mpogue2/ladybug-mixer/docs/3.5mm stereo jacks.png

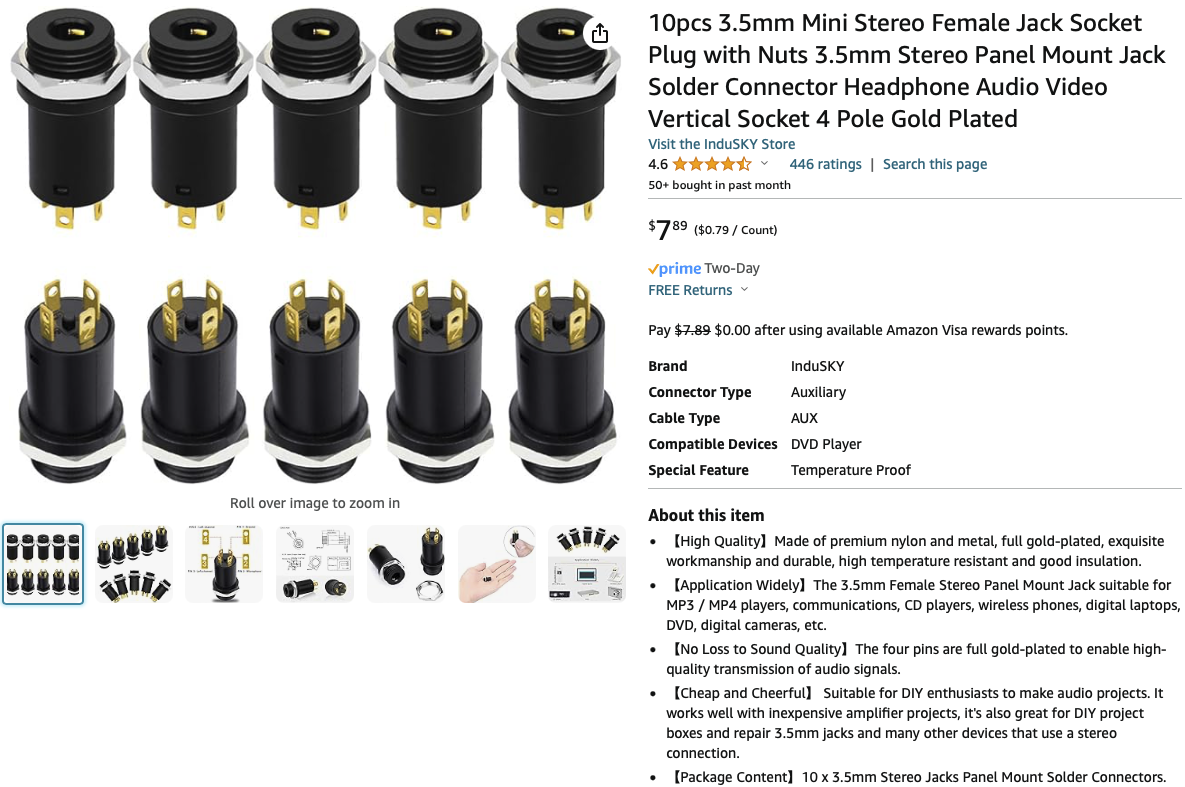
docs/3.5mm stereo jacks.png
