mpogue2/ladybug-mixer/docs/9V Battery Box.png

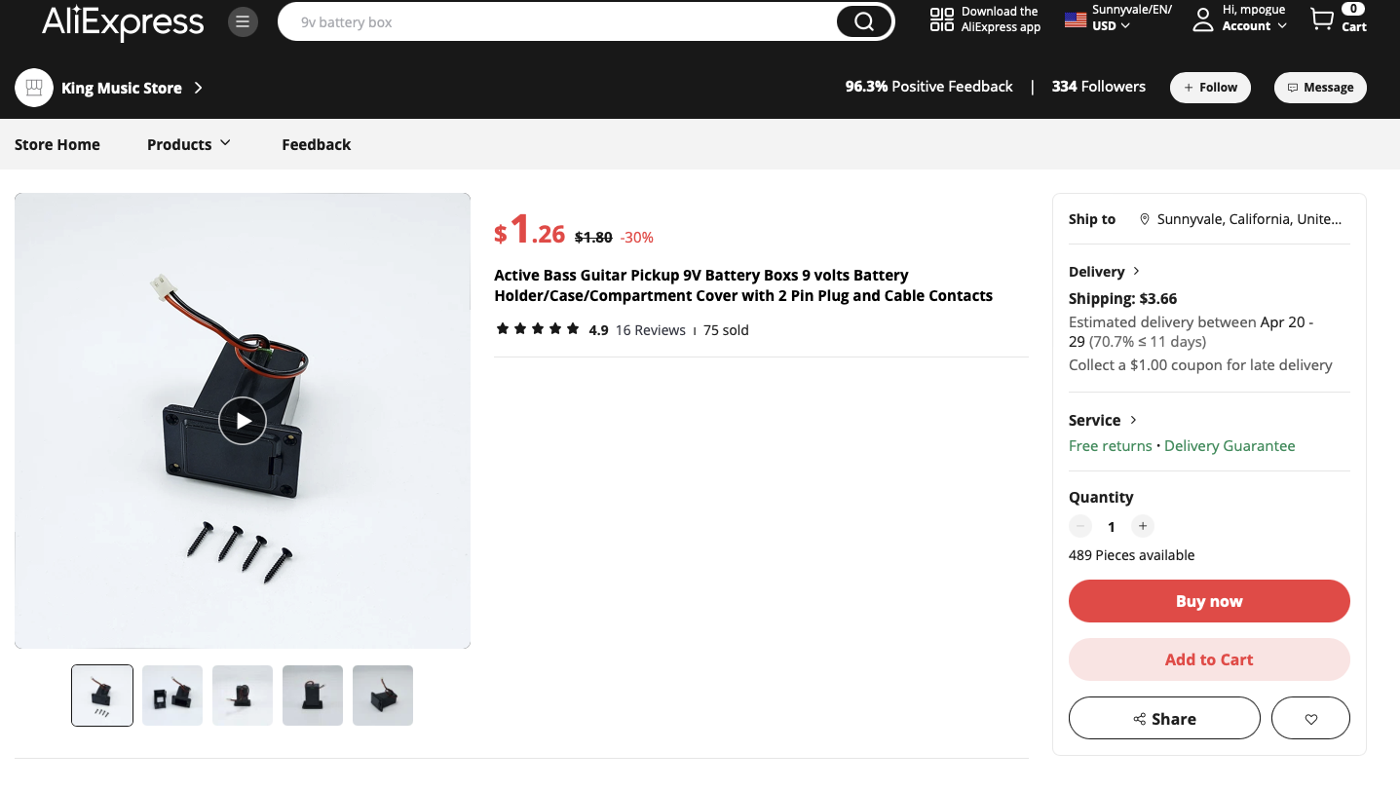
docs/9V Battery Box.png
