mpogue2/ladybug-mixer/docs/100K pots.png

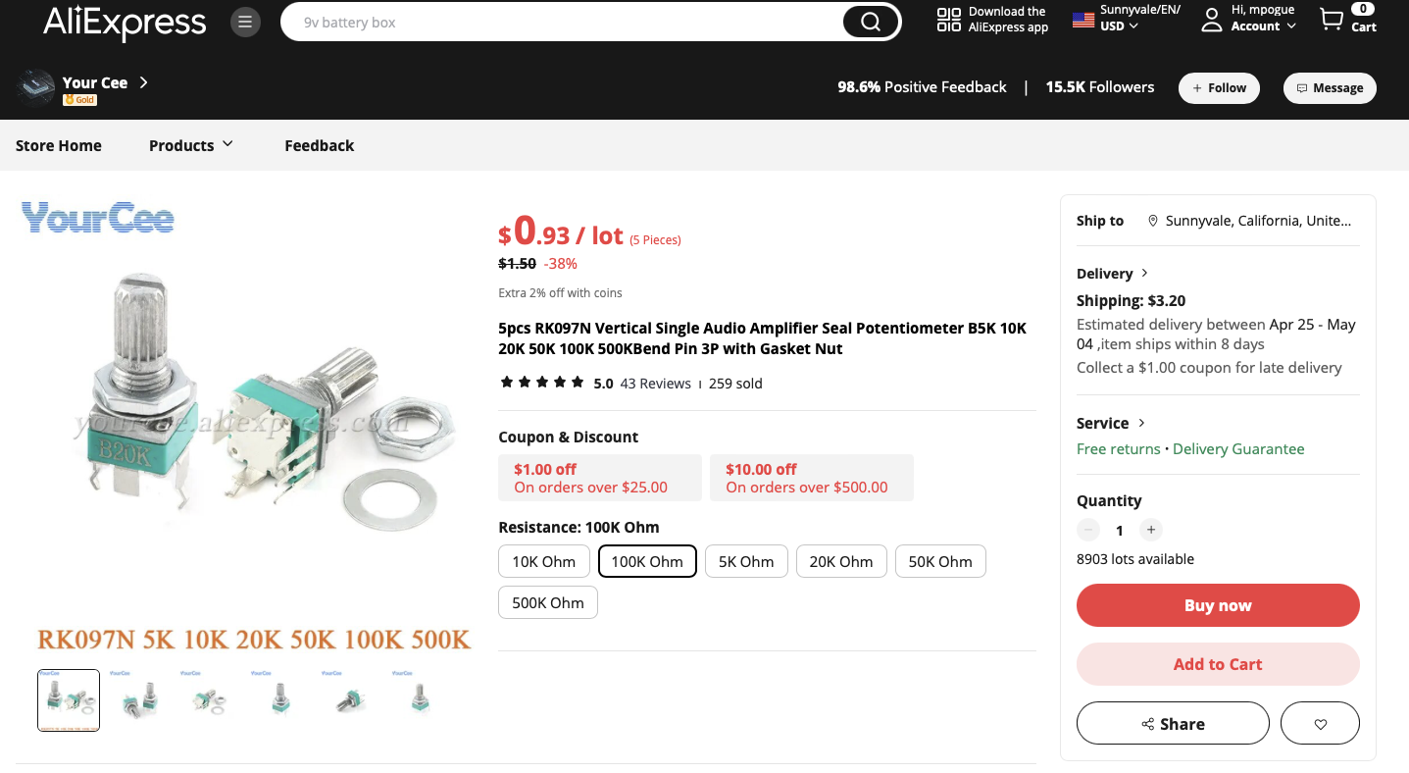
docs/100K pots.png
