mpogue2/ladybug-mixer/docs/AMZN Basics 9V Alkaline batteries.png

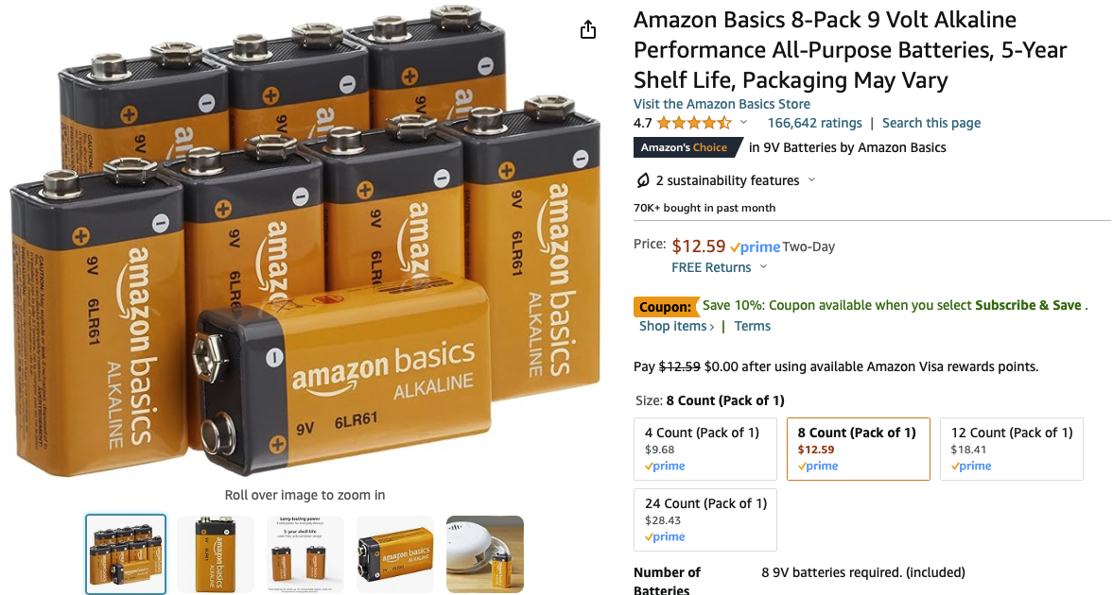
docs/AMZN Basics 9V Alkaline batteries.png
