mpogue2/ladybug-mixer/docs/Neutrik NC3MAV-0 output connector.png

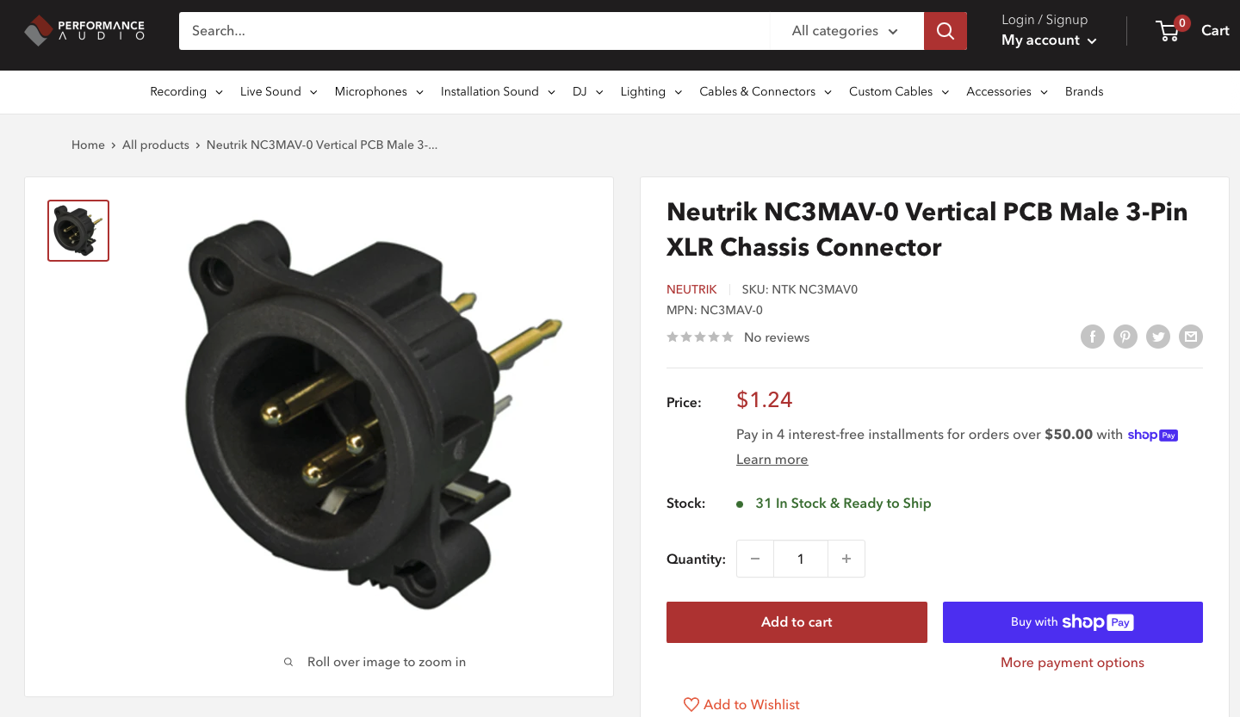
docs/Neutrik NC3MAV-0 output connector.png
