mpogue2/ladybug-mixer/docs/PantherKill knobs.png

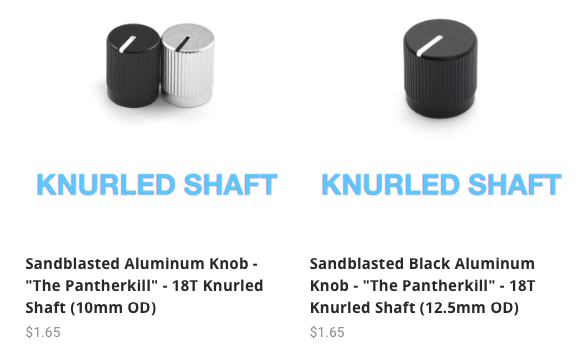
docs/PantherKill knobs.png
