mpogue2/ladybug-mixer/docs/Programmer for STC8G.png

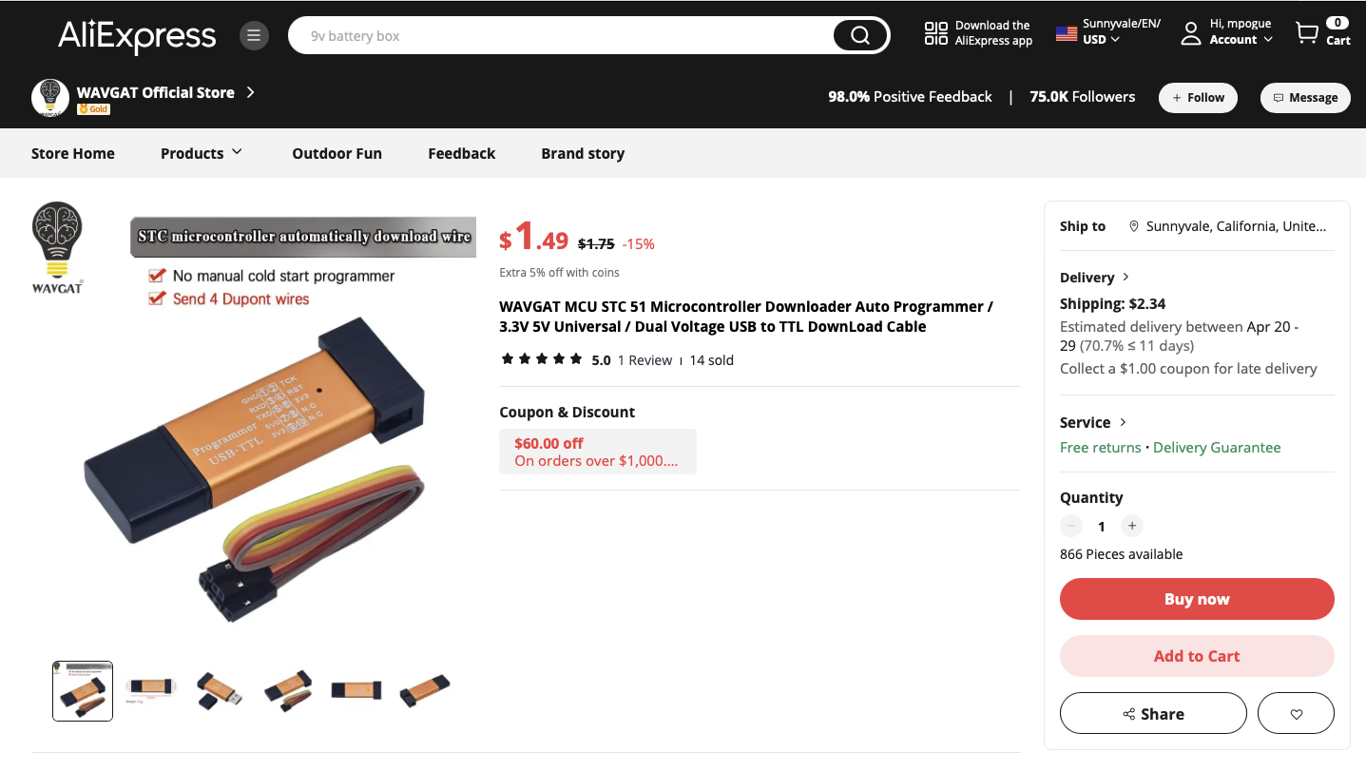
docs/Programmer for STC8G.png
