mpogue2/ladybug-mixer/docs/Rocker switch for power.png

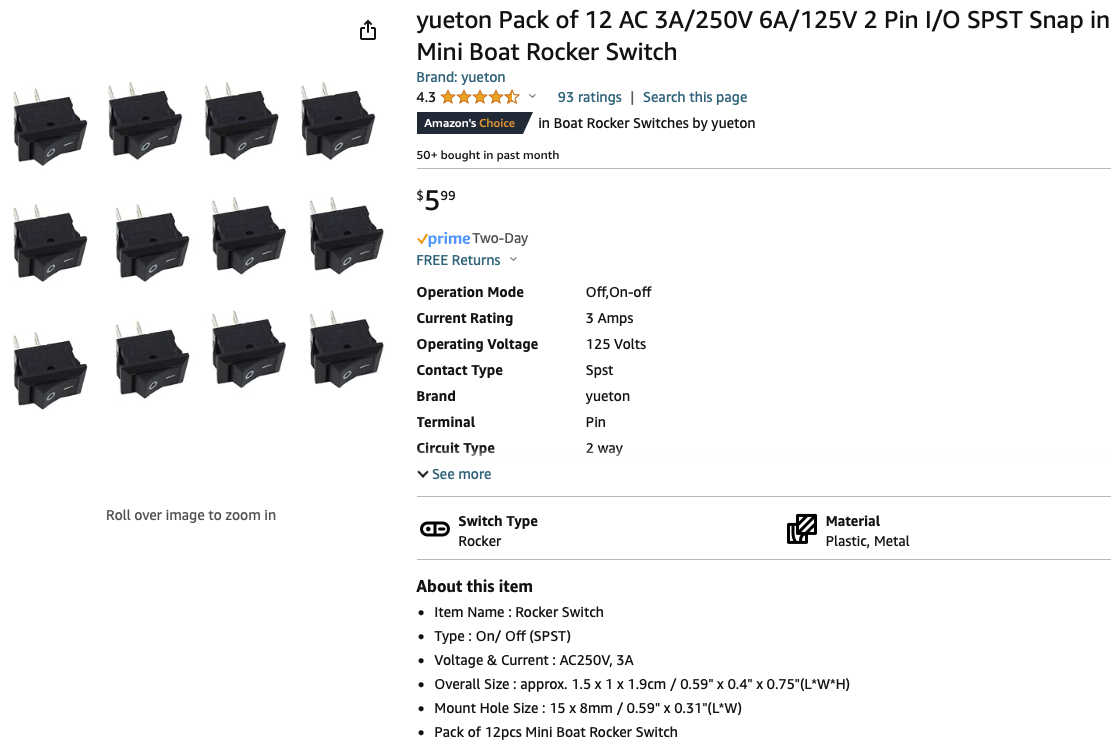
docs/Rocker switch for power.png
