mpogue2/ladybug-mixer/docs/Slide switch for music.png

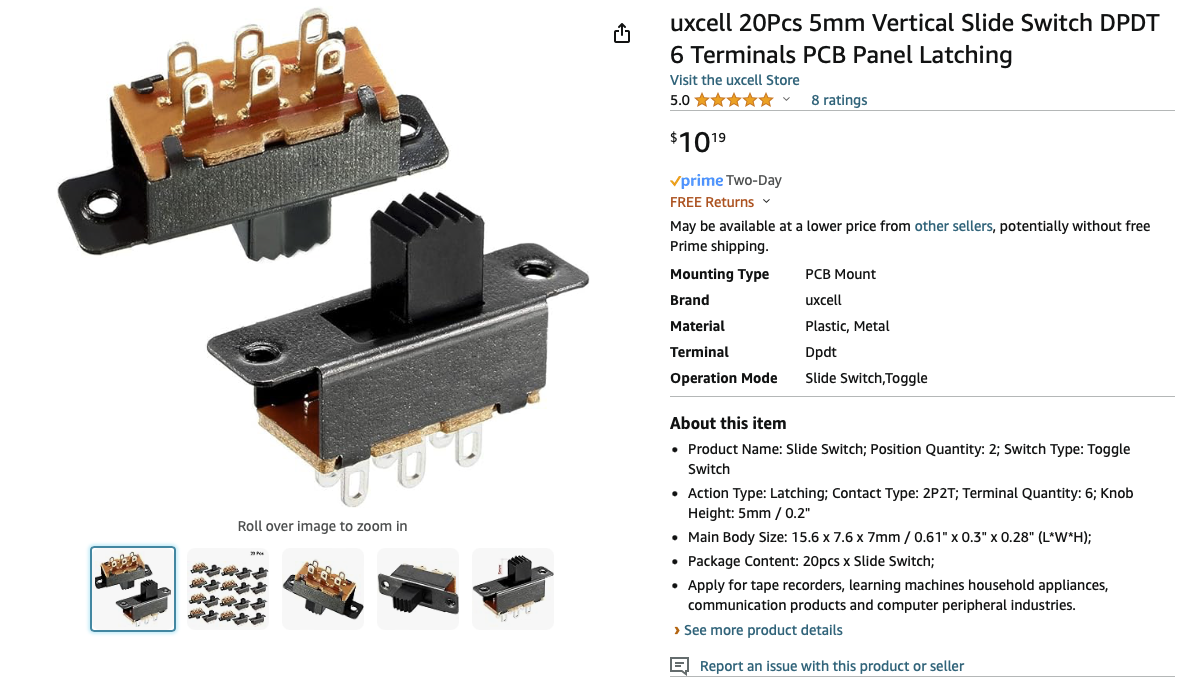
docs/Slide switch for music.png
