mpogue2/ladybug-mixer/docs/Tenergy 9V Lithium batteries.png

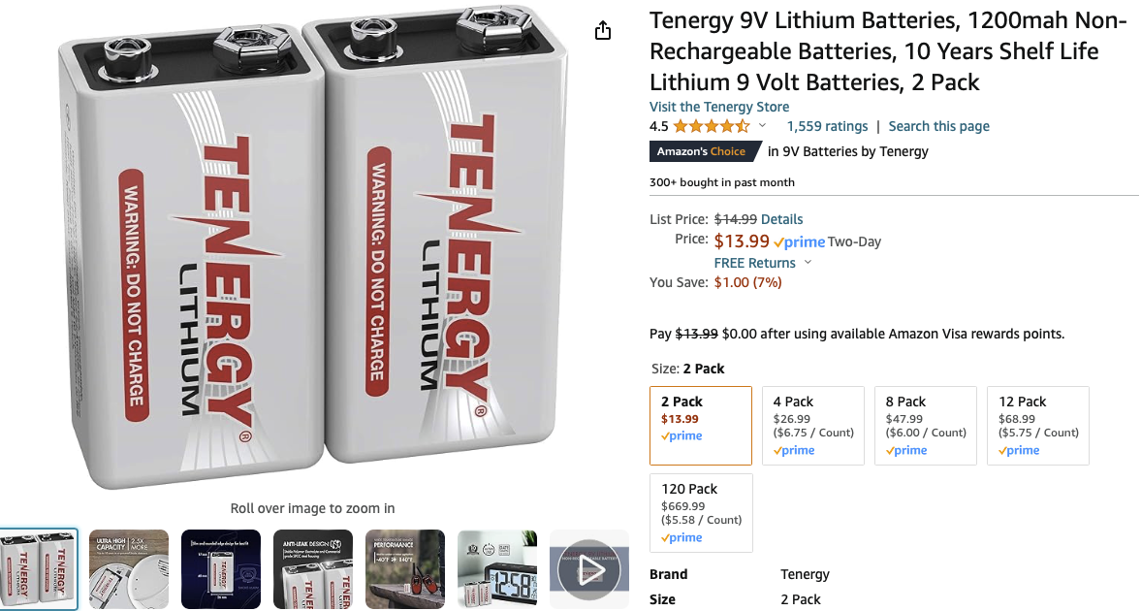
docs/Tenergy 9V Lithium batteries.png
