mpogue2/ladybug-mixer/docs/USB rechargeable 9V batteries.png

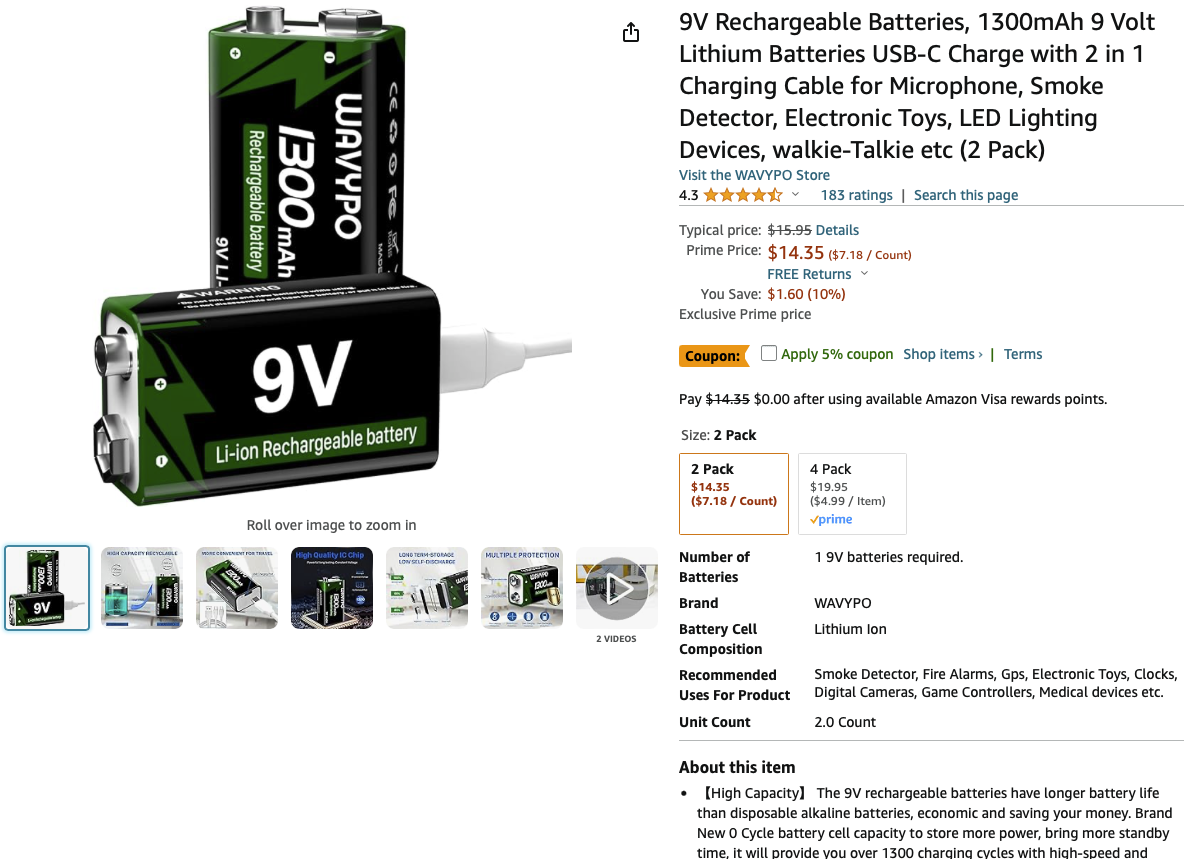
docs/USB rechargeable 9V batteries.png
