mpogue2/ladybug-mixer/docs/White 3mm LEDs.png

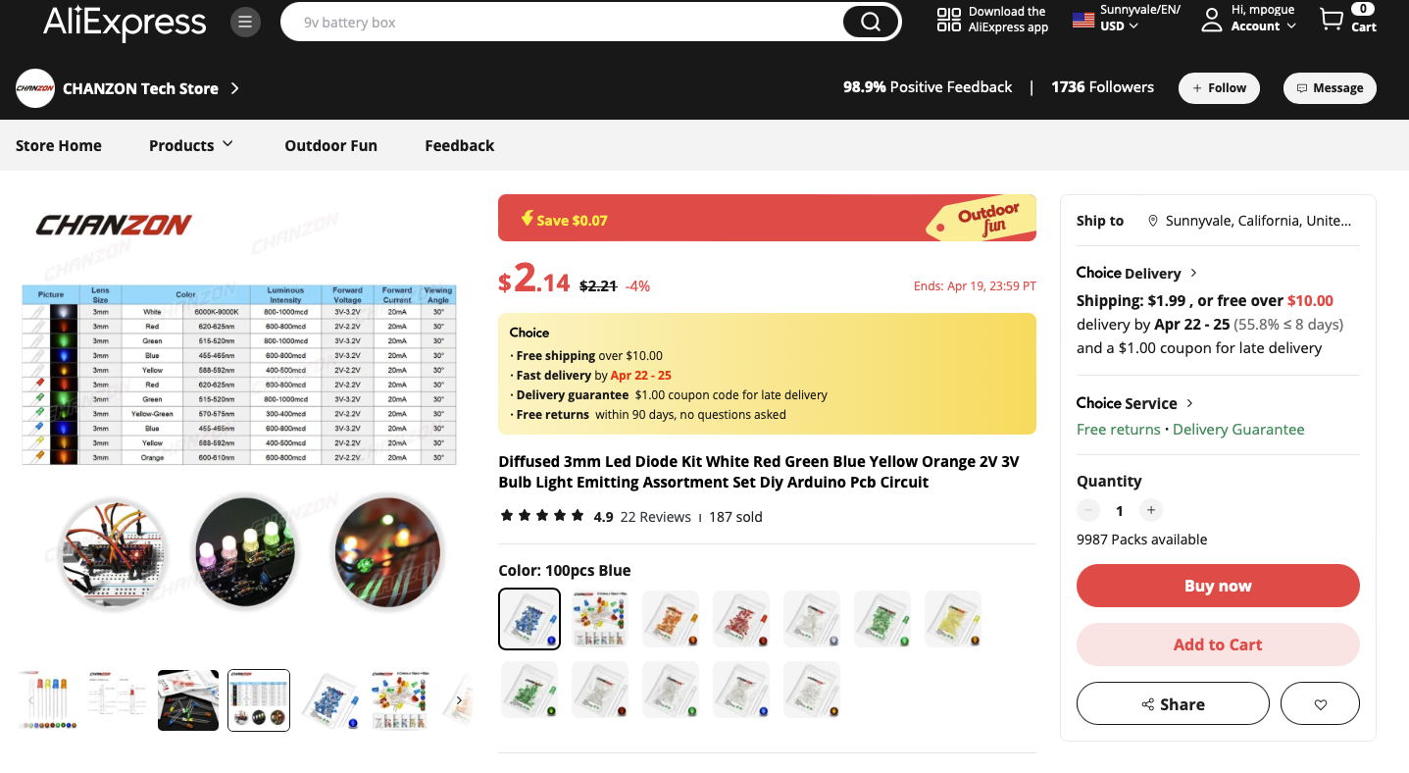
docs/White 3mm LEDs.png
