mpogue2/ladybug-mixer/LB-102/graphics/cutsheet/frame.png

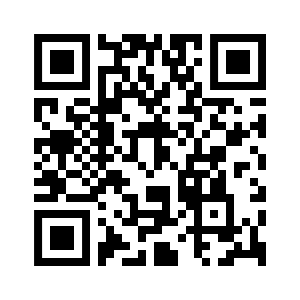
LB-102/graphics/cutsheet/frame.png
