mpogue2/ladybug-mixer/pics/Case_V3_front.jpeg

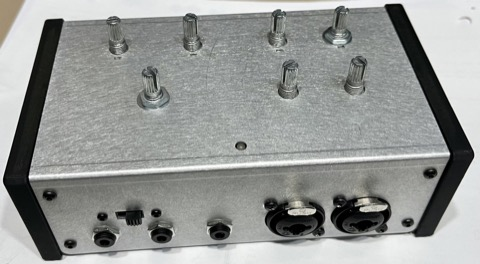
pics/Case_V3_front.jpeg
