mpogue2/ladybug-mixer/pics/Case_V3_rear.jpeg

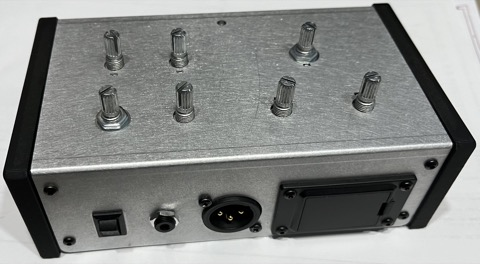
pics/Case_V3_rear.jpeg
