mpogue2/ladybug-mixer/pics/Case_V3_with_knobs.jpeg

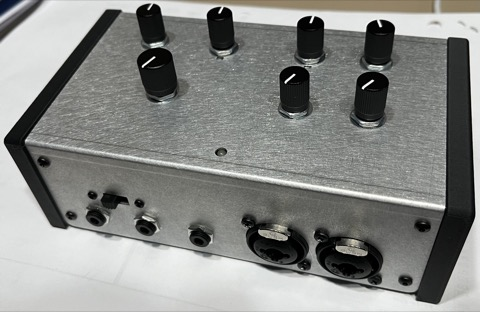
pics/Case_V3_with_knobs.jpeg
