mpogue2/ladybug-mixer/pics/engraving/Brushed_plus_CerMark_1mmps_power100.png

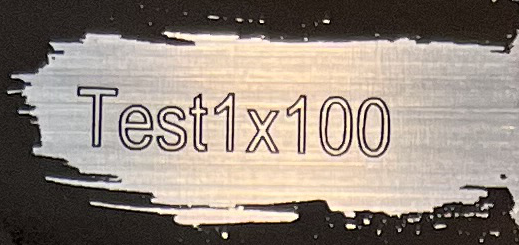
pics/engraving/Brushed_plus_CerMark_1mmps_power100.png
