mpogue2/ladybug-mixer/pics/engraving/Deburred_plus_CerMark_124mmps_power100.png

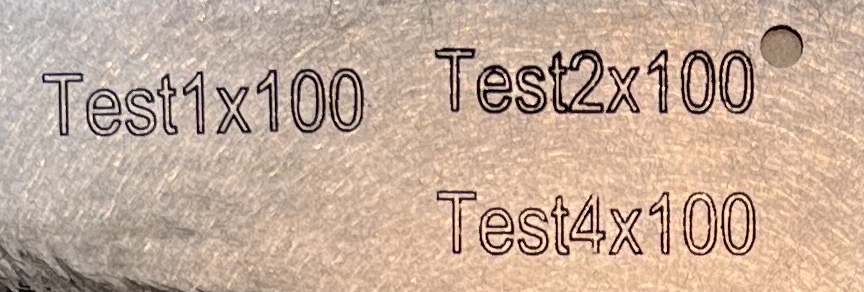
pics/engraving/Deburred_plus_CerMark_124mmps_power100.png
