mpogue2/ladybug-mixer/pics/engraving/fiberLaserEngraved_Brushed5052Al.png

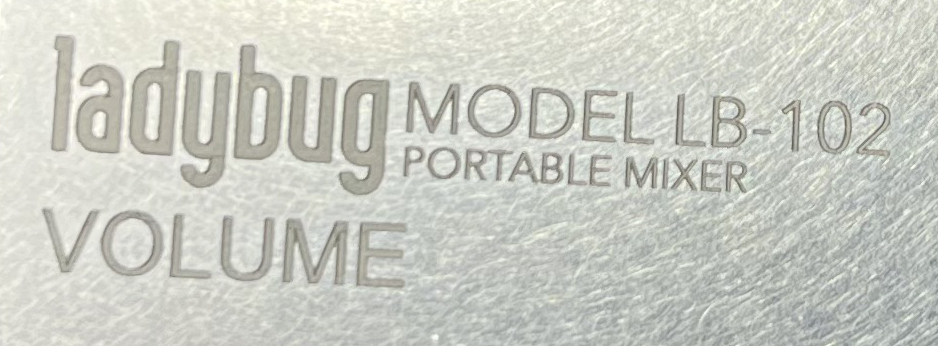
pics/engraving/fiberLaserEngraved_Brushed5052Al.png
