mpogue2/ladybug-mixer/pics/engraving/fiberLaserEngraved_PLA_bottom.png

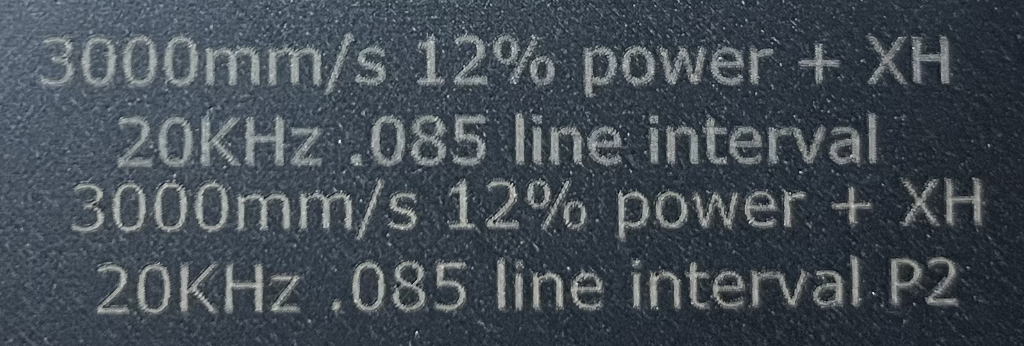
pics/engraving/fiberLaserEngraved_PLA_bottom.png
