mpogue2/ladybug-mixer/pics/engraving/fiberLaserEngraved_PowderCoated1018Steel.png

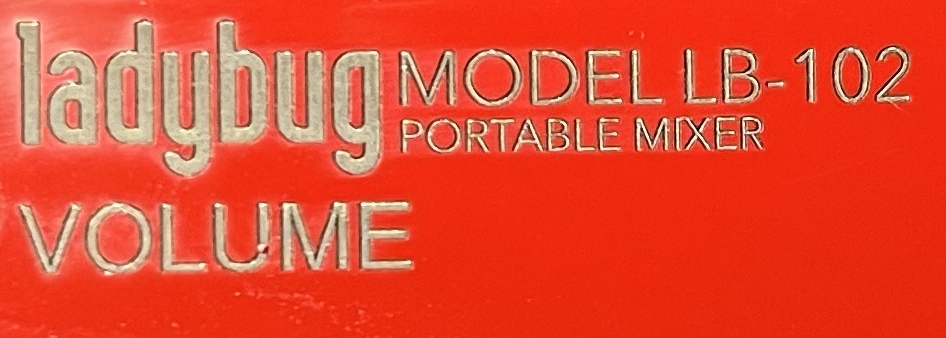
pics/engraving/fiberLaserEngraved_PowderCoated1018Steel.png
