mpogue2/ladybug-mixer/pics/engraving/fiberLaserEngraved_PowderCoated5052Al.png

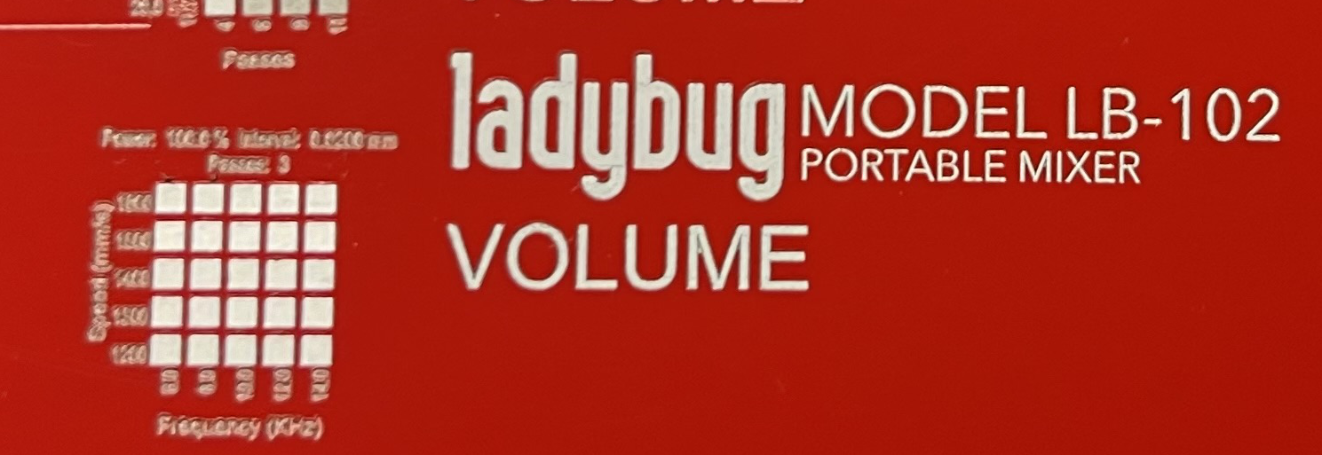
pics/engraving/fiberLaserEngraved_PowderCoated5052Al.png
