mpogue2/ladybug-mixer/pics/engraving/fiberLaserEngraved_top.png

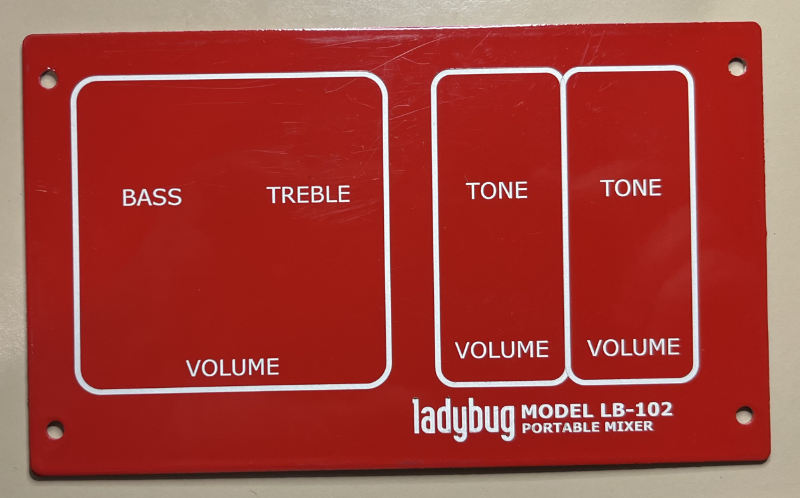
pics/engraving/fiberLaserEngraved_top.png
