mpogue2/ladybug-mixer/pics/engraving/Final_fiber_laser_settings.png

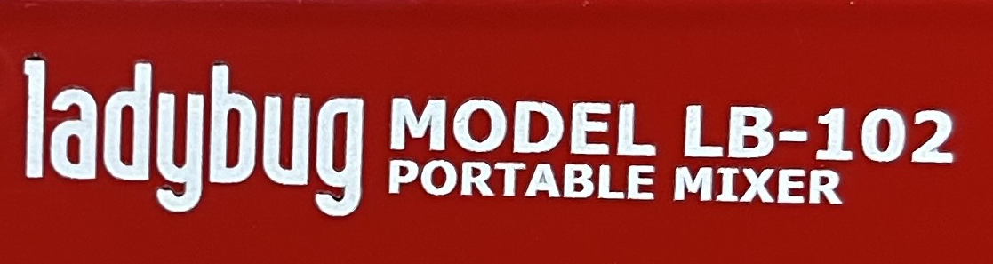
pics/engraving/Final_fiber_laser_settings.png
