mpogue2/ladybug-mixer/pics/engraving/painted_cut_text_250.png

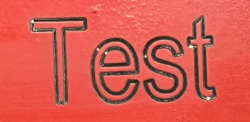
pics/engraving/painted_cut_text_250.png
