mpogue2/ladybug-mixer/pics/engraving/painted_rasterized_text_250.png

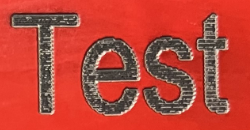
pics/engraving/painted_rasterized_text_250.png
