mpogue2/ladybug-mixer/pics/Inside_PCB_V2.4.jpeg

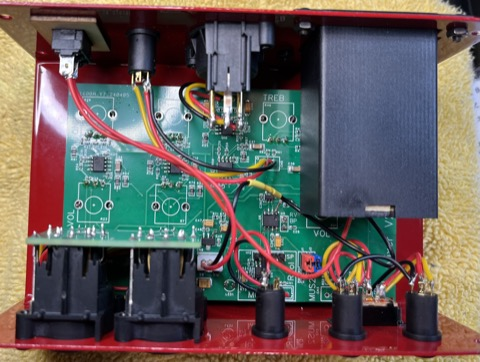
pics/Inside_PCB_V2.4.jpeg
