mpogue2/ladybug-mixer/pics/Main_PCB_V2.2.jpeg

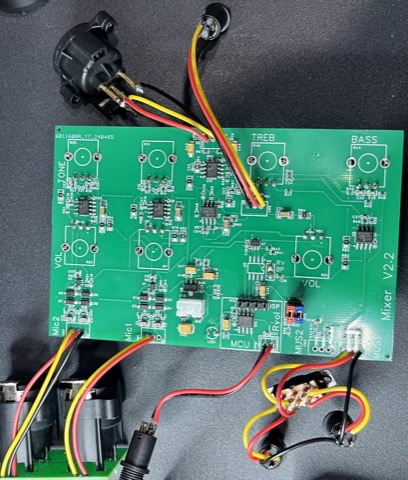
pics/Main_PCB_V2.2.jpeg
