mpogue2/ladybug-mixer/pics/MainBoard_V2.2.jpeg

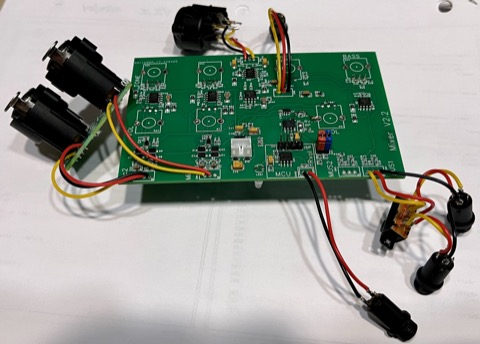
pics/MainBoard_V2.2.jpeg
