mpogue2/ladybug-mixer/pics/RandomOrbitalSander.png

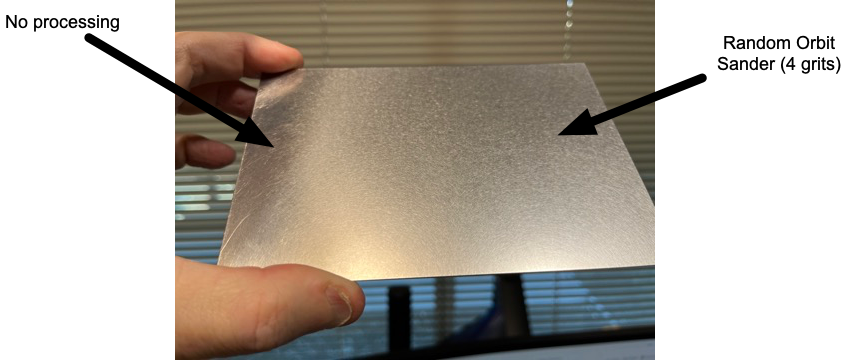
pics/RandomOrbitalSander.png
