mpogue2/ladybug-mixer/pics/ThreadedInserts.jpg

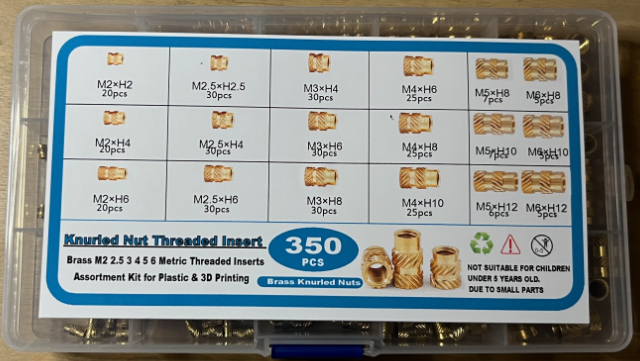
pics/ThreadedInserts.jpg
