mpogue2/ladybug-mixer/pics/V3_All.jpeg

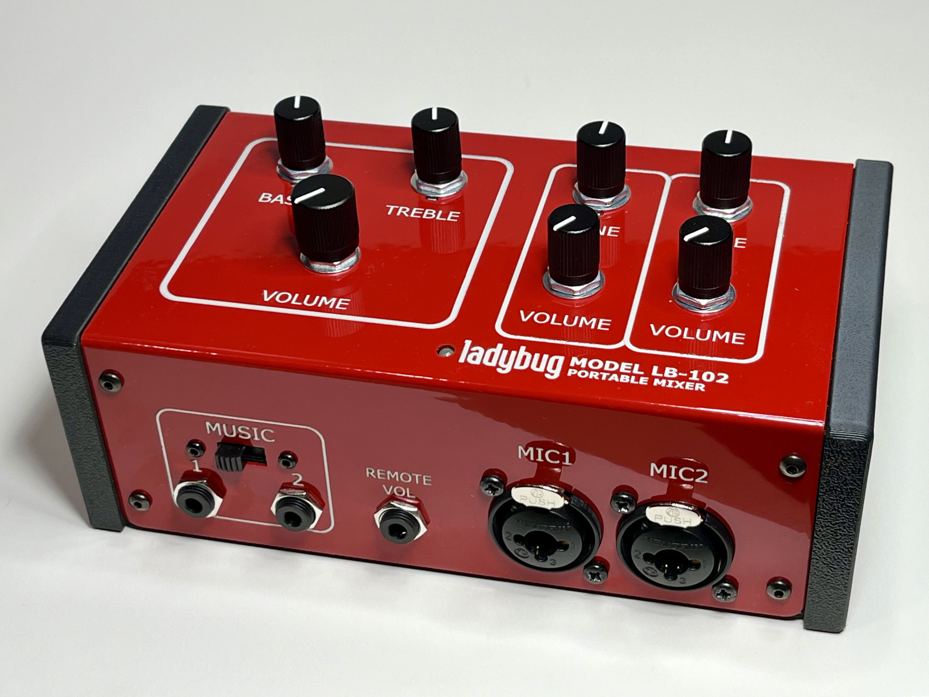
pics/V3_All.jpeg
