mpogue2/ladybug-mixer/pics/V3_Back.jpeg

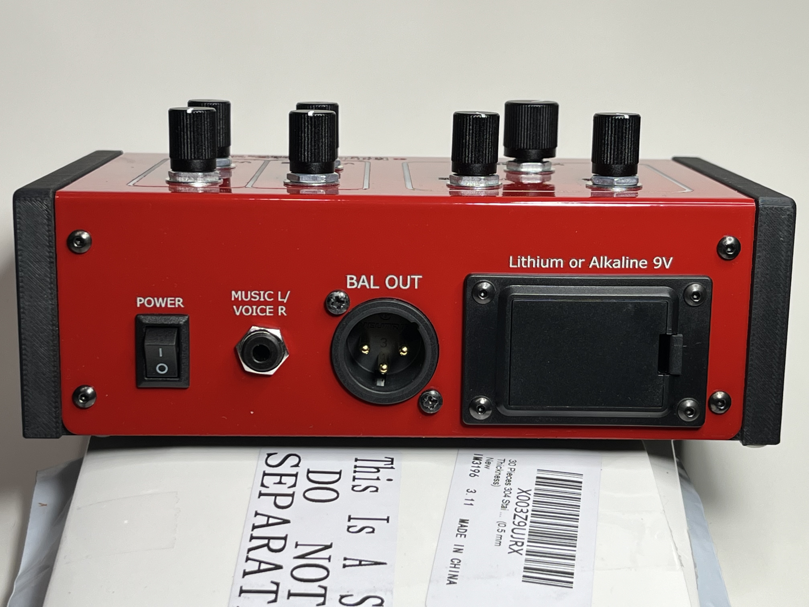
pics/V3_Back.jpeg
