mpogue2/ladybug-mixer/pics/V3_Top.jpeg

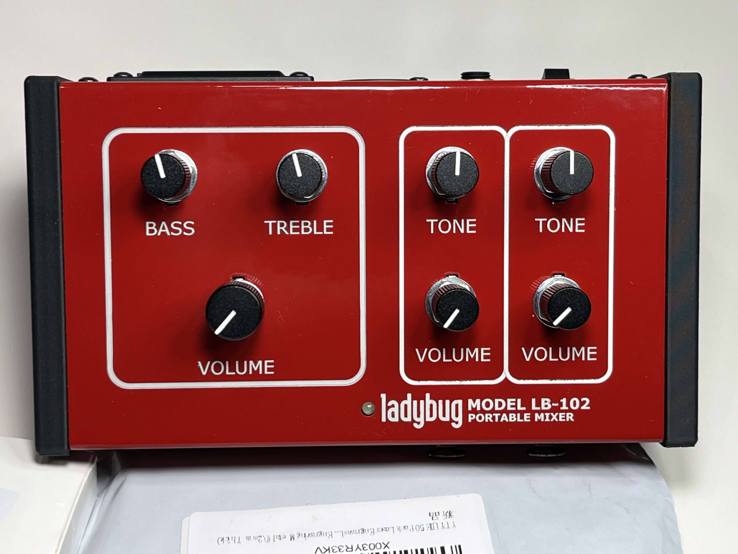
pics/V3_Top.jpeg
