mpogue2/ladybug-mixer/pics/Weller_tip_for_inserts.jpg

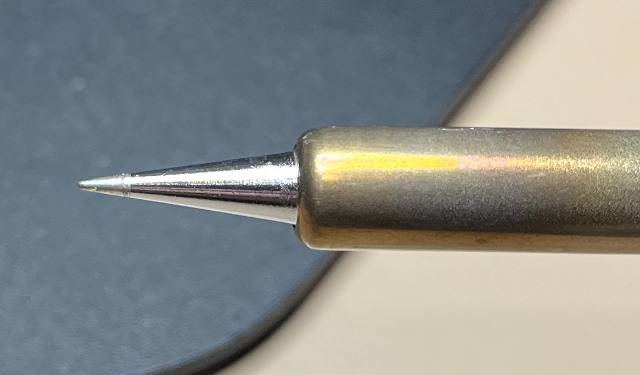
pics/Weller_tip_for_inserts.jpg
