mpogue2/ladybug-mixer/LB-102/V4/Software/MCU_firmware/src/Hilton RVC Volume Curve Measured.png

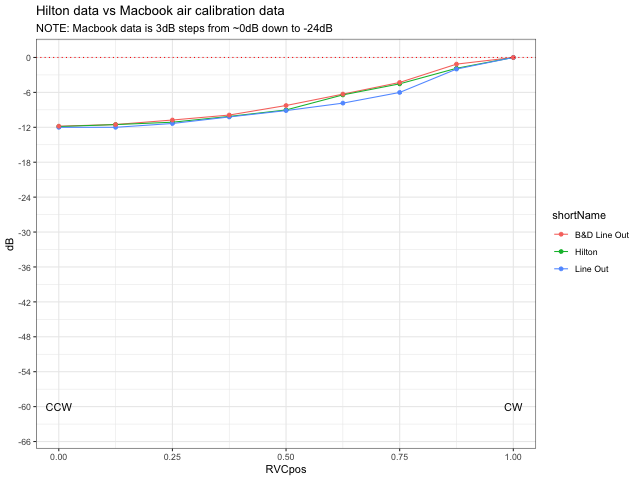
LB-102/V4/Software/MCU_firmware/src/Hilton RVC Volume Curve Measured.png
