mpogue2/ladybug-mixer/tests/BandwidthAndEQ/HiltonMA220_Aux1.png

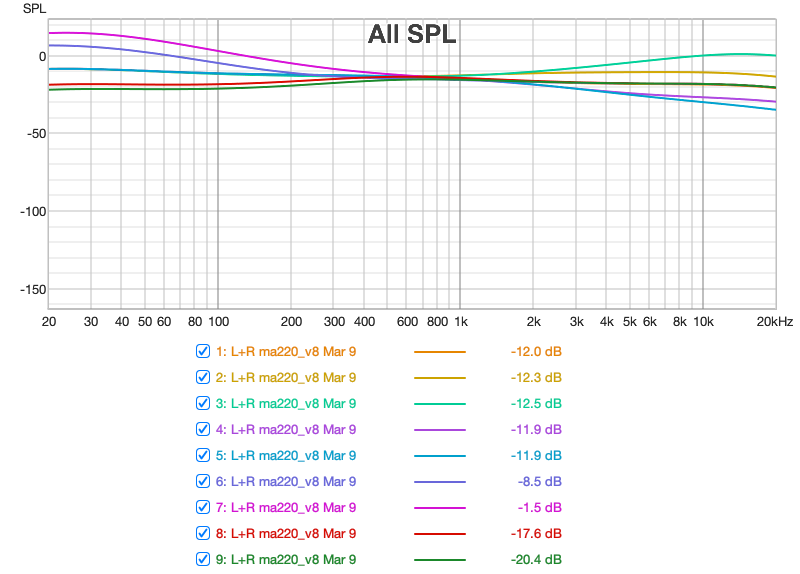
tests/BandwidthAndEQ/HiltonMA220_Aux1.png
