mpogue2/ladybug-mixer/tests/BandwidthAndEQ/HiltonMA220_Mic2.png

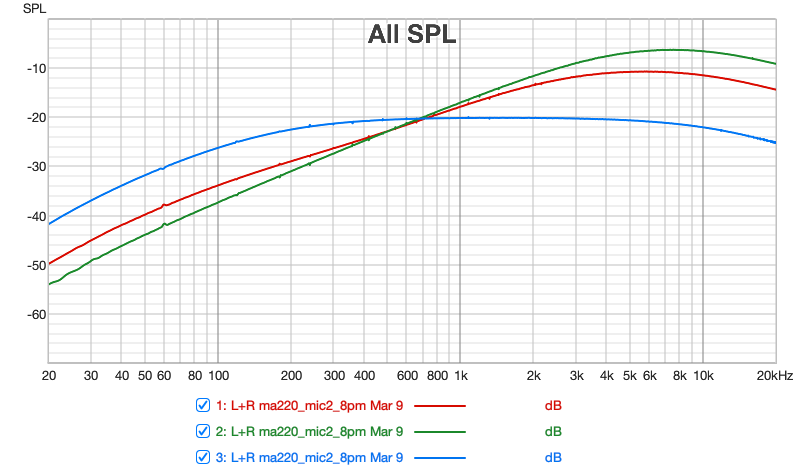
tests/BandwidthAndEQ/HiltonMA220_Mic2.png
