mpogue2/ladybug-mixer/tests/BandwidthAndEQ/V2_Mic1 vs Mic2 Bandwidth.png

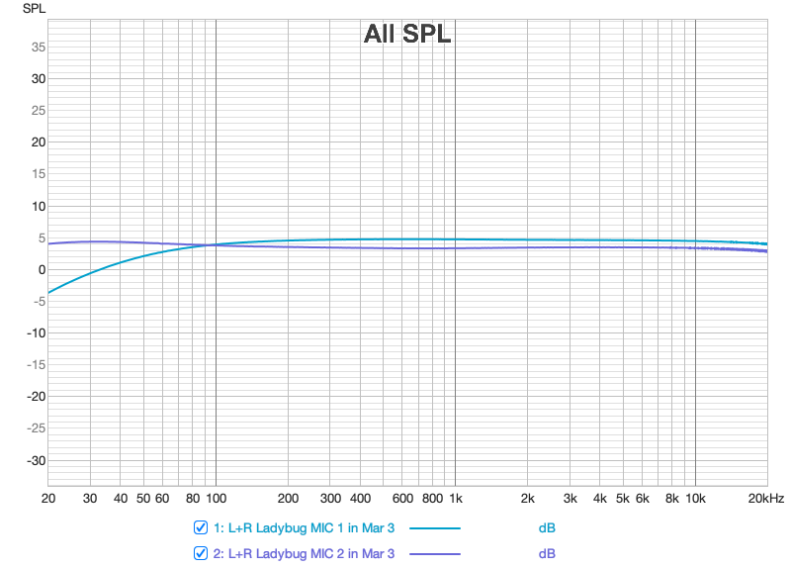
tests/BandwidthAndEQ/V2_Mic1 vs Mic2 Bandwidth.png
