mpogue2/ladybug-mixer/tests/BandwidthAndEQ/V2_Mic1.png

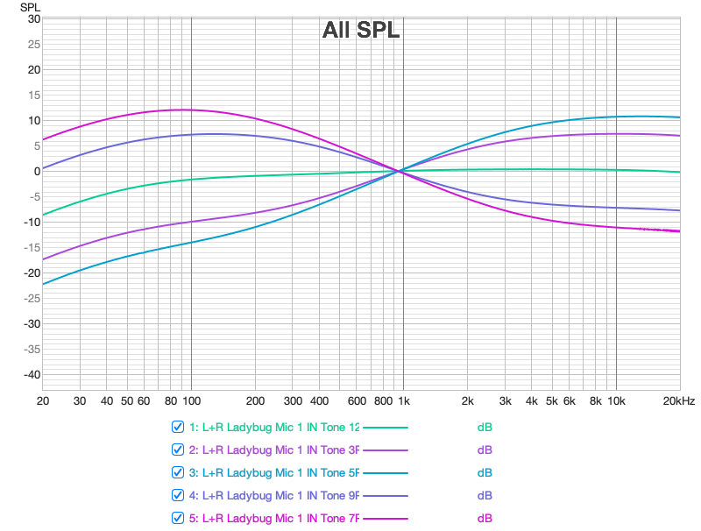
tests/BandwidthAndEQ/V2_Mic1.png
