mpogue2/ladybug-mixer/tests/BatteryLife/V2_batteryLife_noRVC.png

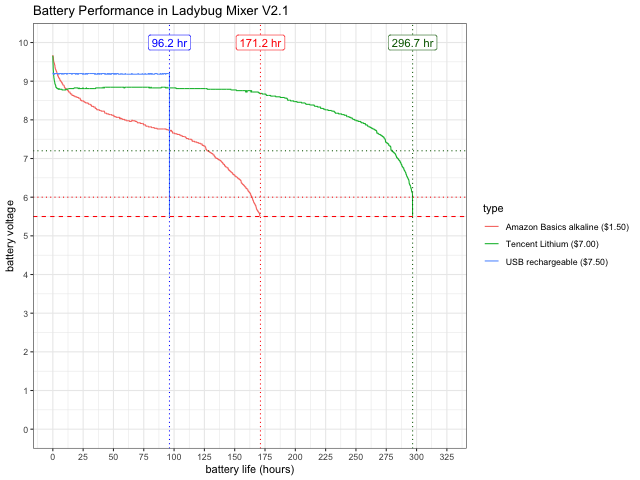
tests/BatteryLife/V2_batteryLife_noRVC.png
