mpogue2/ladybug-mixer/tests/Noise/V2_Mic1 vs Mic2 base level noise.png

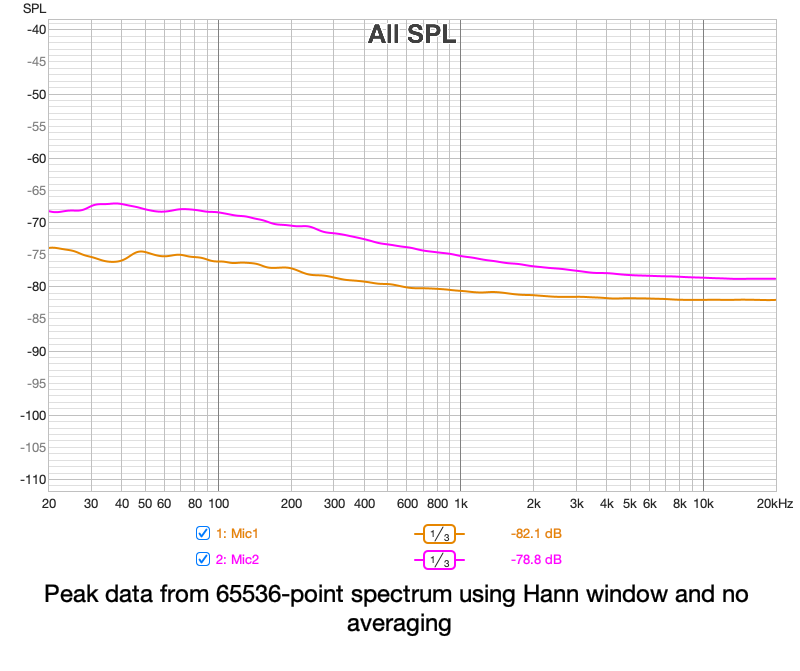
tests/Noise/V2_Mic1 vs Mic2 base level noise.png
