mpogue2/ladybug-mixer/LB-102/V4/Main Board/SCH_mixer project v2.4_2024-08-26.pdf

# Microphone preamp, Mic #1

# Single "Tilt" (+/-16dB)

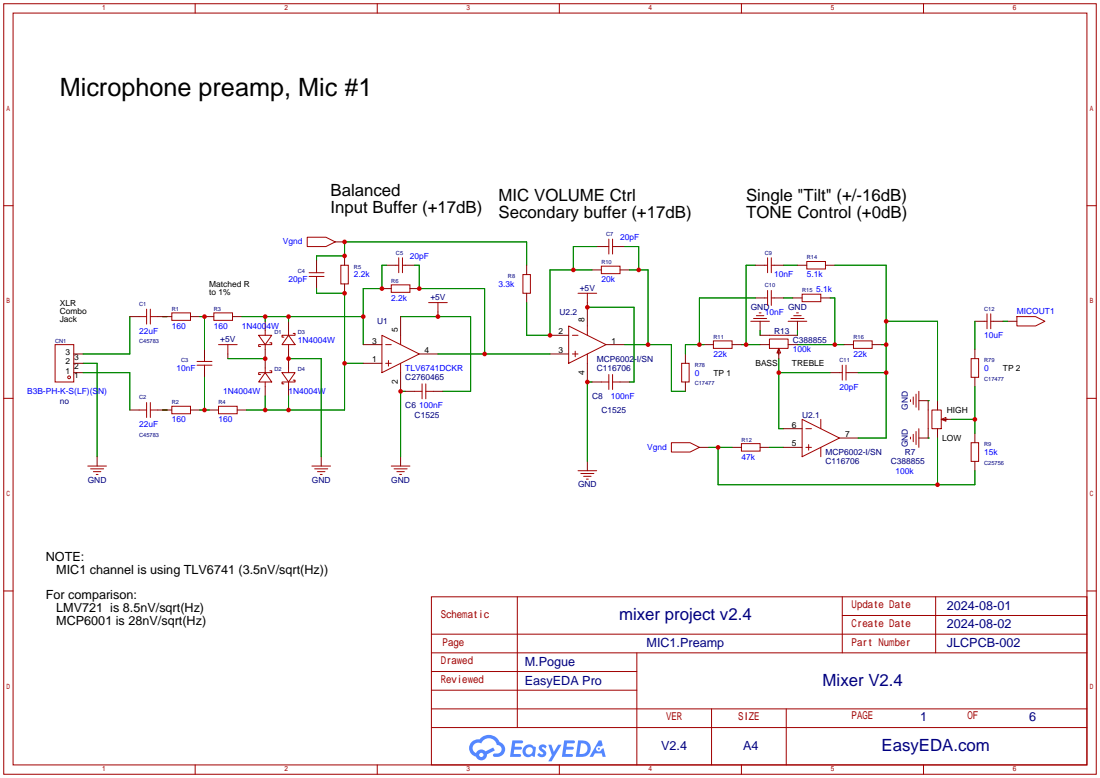
[picture p71: page 1]

NOTE:
MIC1 channel is using TLV6741 (3.5nV/sqrt(Hz))
For comparison:
LMV721 is 8.5nV/sqrt(Hz)
MCP6001 is 28nV/sqrt(Hz)

# Microphone preamp, Mic #2

# Single "Tilt" (+/-16dB)

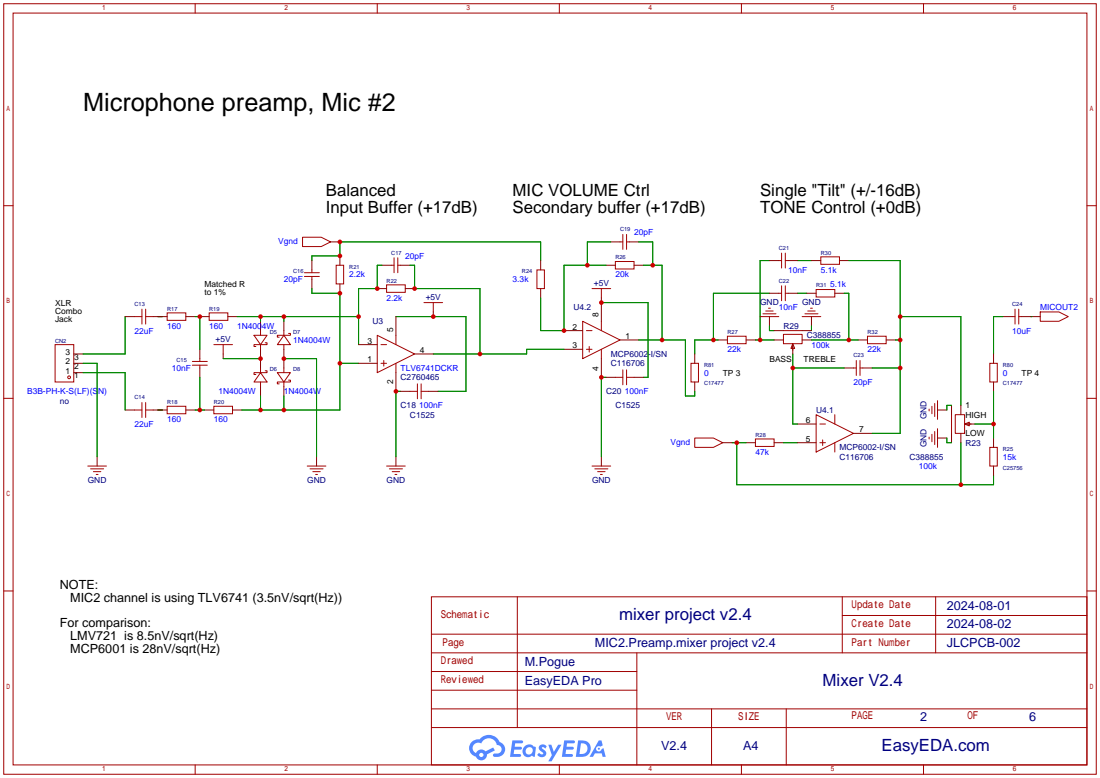
[picture p72: page 2]

NOTE:
MIC2 channel is using TLV6741 (3.5nV/sqrt(Hz))
For comparison:
LMV721 is 8.5nV/sqrt(Hz)
MCP6001 is 28nV/sqrt(Hz)

# Music Mixer/Preamp/Remote Vol/Main Vol Control

(source: https://www.ti.com/lit/ug/tidu034/tidu034.pdf, https://sound-au.com/project01.htm,

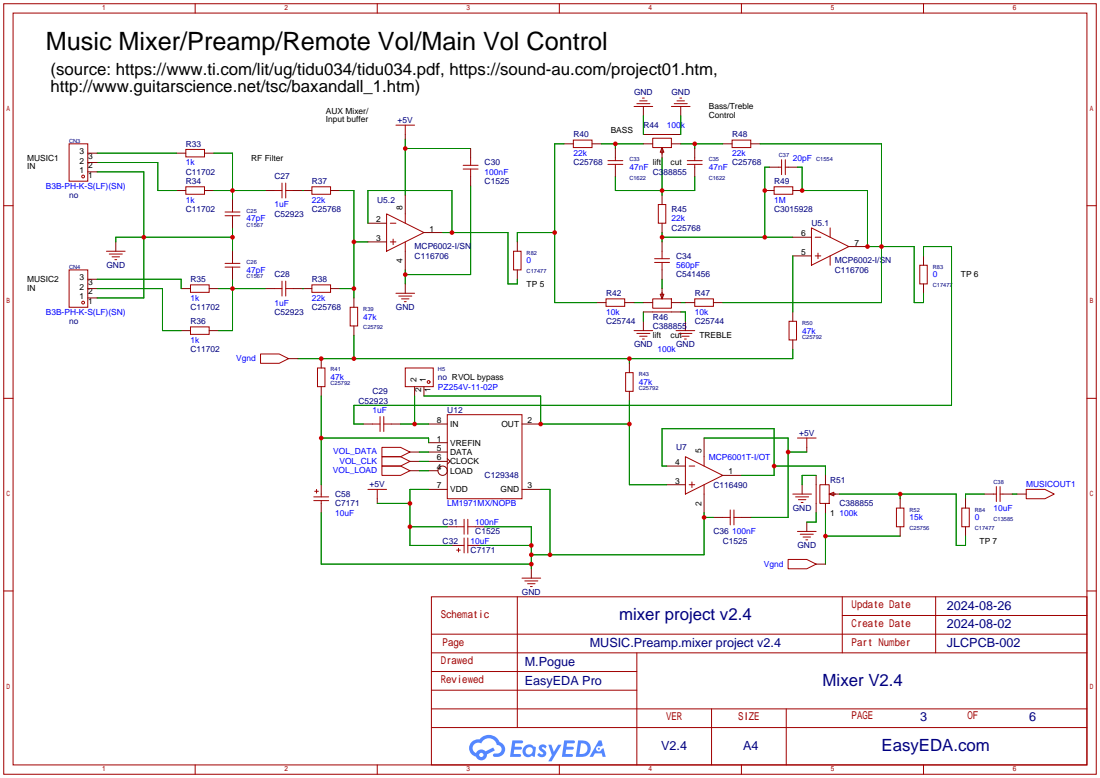
[picture p73: page 3]

http://www.guitarscience.net/tsc/baxandall_1.htm)

2024-08-02 mixer project v2.4
MUSIC.Preamp.mixer project v2.4

# Final Mixer/Balanced output driver

# Voice/Music Mixer Voice Mixer &

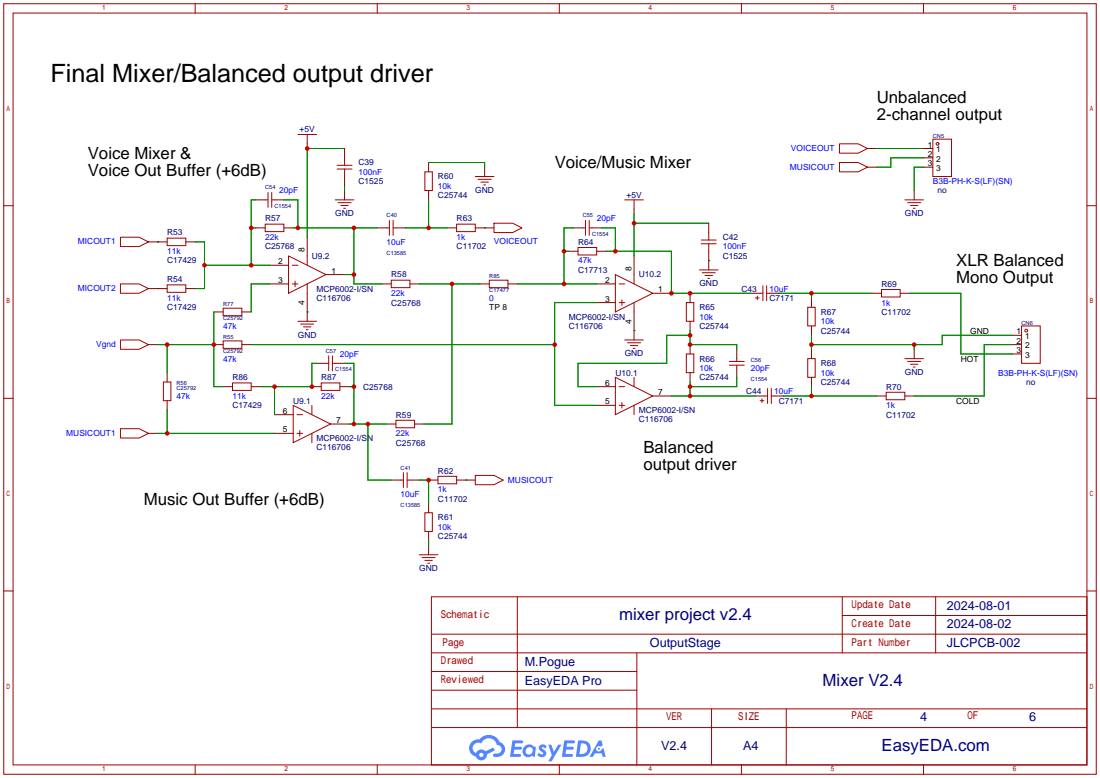
[picture p74: page 4]

# Input Power Management

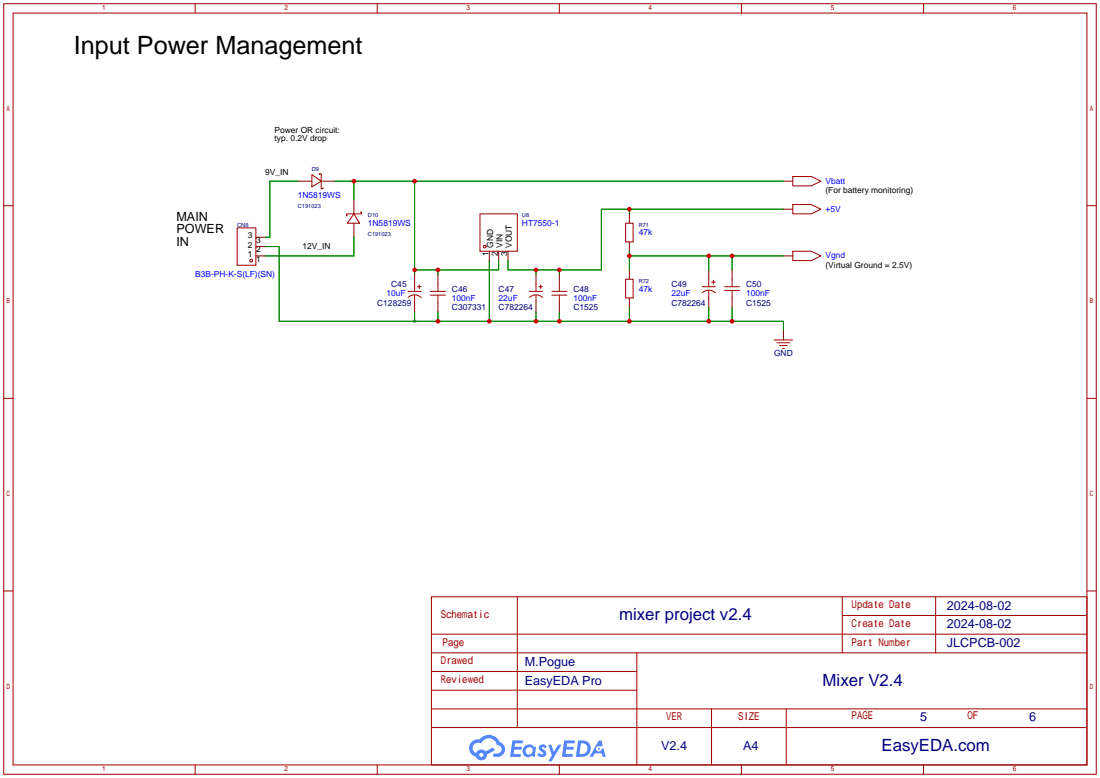
[picture p75: page 5]

# MCU (Battery Monitor, Remote Vol Ctrl)

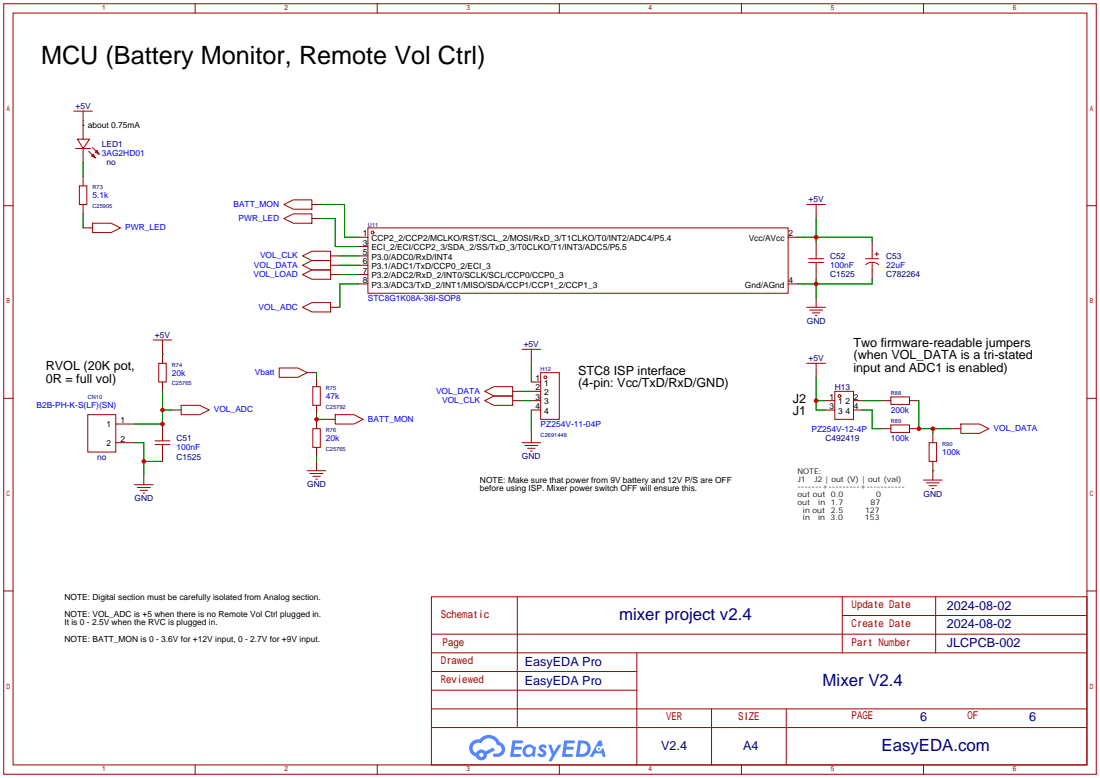
[picture p76: page 6]

GND
Two firmware-readable jumpers
(when VOL_DATA is a tri-stated
input and ADC1 is enabled)

STC8 ISP interface
(4-pin: Vcc/TxD/RxD/GND)

NOTE: Make sure that power from 9V battery and 12V P/S are OFF
before using ISP. Mixer power switch OFF will ensure this.

NOTE: Digital section must be carefully isolated from Analog section.
NOTE: VOL_ADC is +5 when there is no Remote Vol Ctrl plugged in.
It is 0 - 2.5V when the RVC is plugged in.
NOTE: BATT_MON is 0 - 3.6V for +12V input, 0 - 2.7V for +9V input.
