mpogue2/ladybug-mixer/LB-102/V2/SCH_mixer project v2.0_2024-02-03.pdf

# Microphone preamp, Mic #1

# Single "Tilt" (+/-16dB)

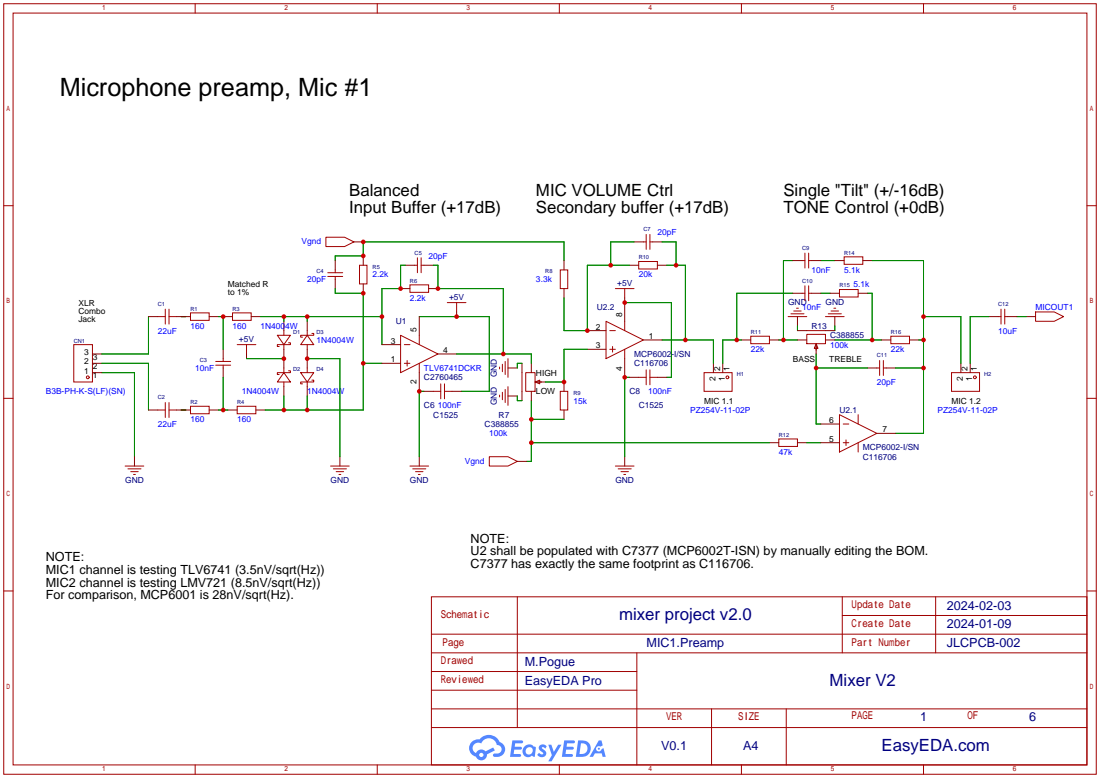
[picture p78: page 1]

MCP6002-I/SN 4
C7377 has exactly the same footprint as C116706. GND GND

NOTE:
U2 shall be populated with C7377 (MCP6002T-ISN) by manually editing the BOM.

MIC1 channel is testing TLV6741 (3.5nV/sqrt(Hz))
MIC2 channel is testing LMV721 (8.5nV/sqrt(Hz))
For comparison, MCP6001 is 28nV/sqrt(Hz).

# Microphone preamp, Mic #2

# Single "Tilt" (+/-16dB)

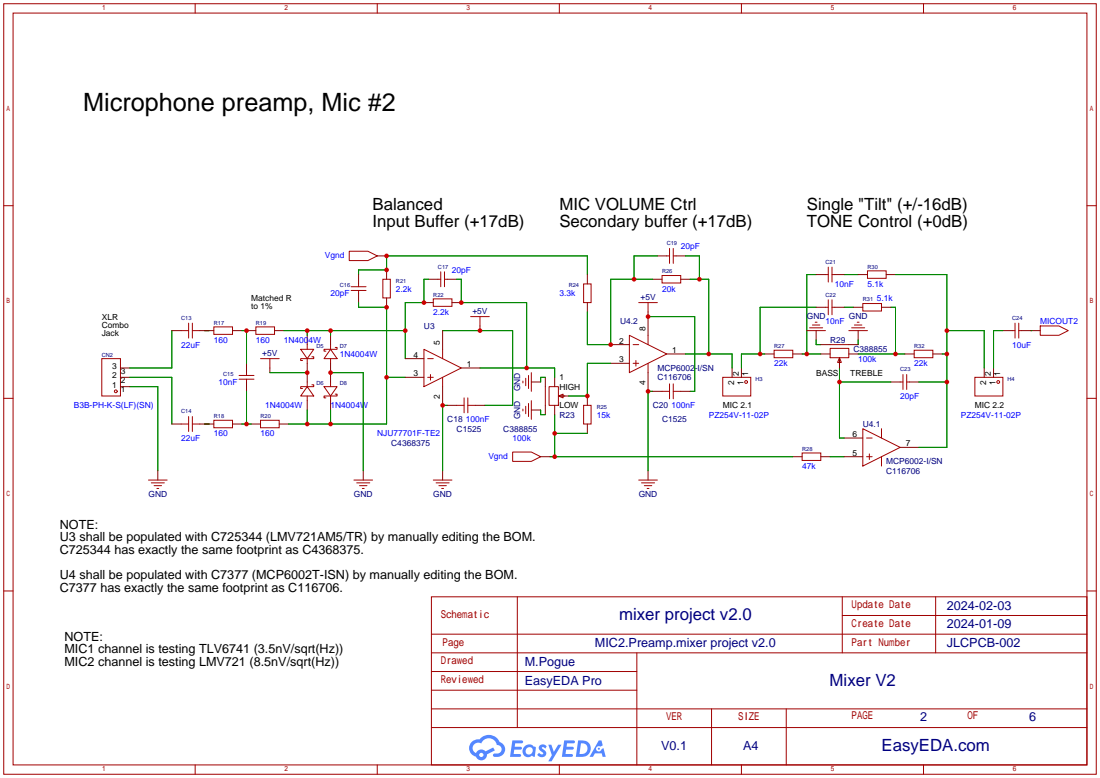
[picture p79: page 2]

NOTE:
U3 shall be populated with C725344 (LMV721AM5/TR) by manually editing the BOM.
C725344 has exactly the same footprint as C4368375.
U4 shall be populated with C7377 (MCP6002T-ISN) by manually editing the BOM.
C7377 has exactly the same footprint as C116706.

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

# Music Mixer/Preamp/Remote Vol/Main Vol Control

(source: https://www.ti.com/lit/ug/tidu034/tidu034.pdf, https://sound-au.com/project01.htm,

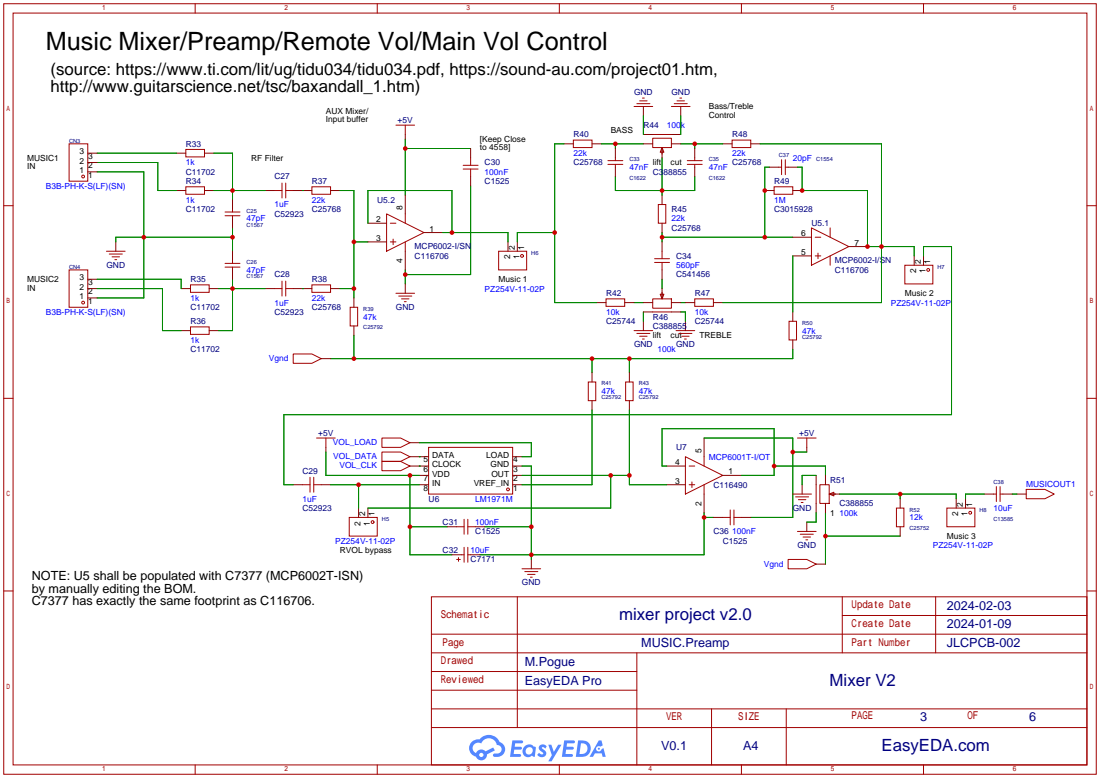
[picture p80: page 3]

http://www.guitarscience.net/tsc/baxandall_1.htm)

NOTE: U5 shall be populated with C7377 (MCP6002T-ISN)
by manually editing the BOM.
C7377 has exactly the same footprint as C116706.

# Final Mixer/Balanced output driver

# Voice/Music Mixer Voice Mixer &

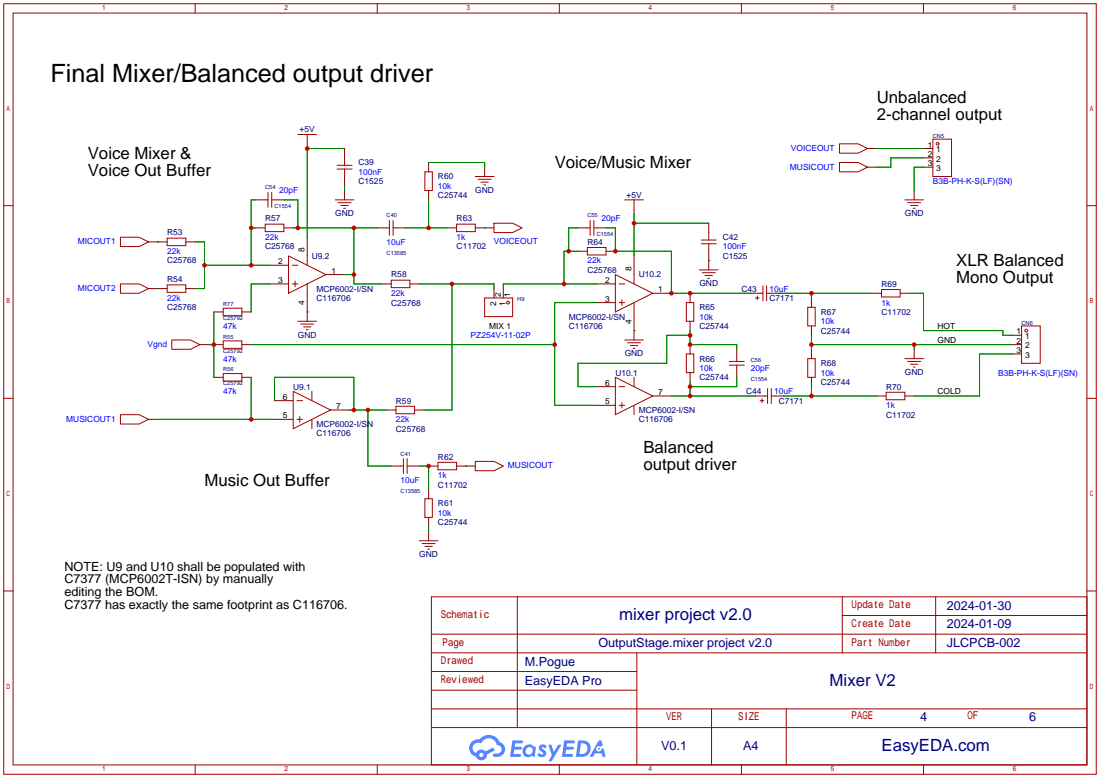
[picture p81: page 4]

NOTE: U9 and U10 shall be populated with
C7377 (MCP6002T-ISN) by manually
editing the BOM.
C7377 has exactly the same footprint as C116706.

# Input Power Management

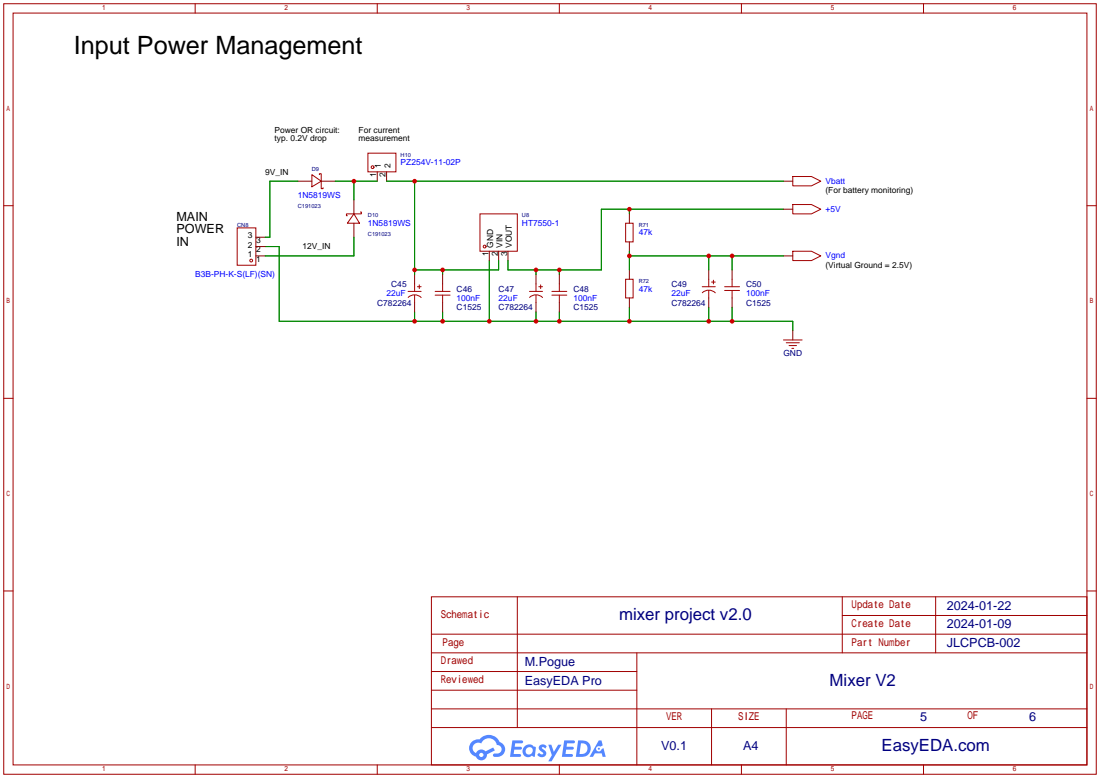
[picture p82: page 5]

# MCU (Battery Monitor, Remote Vol Ctrl)

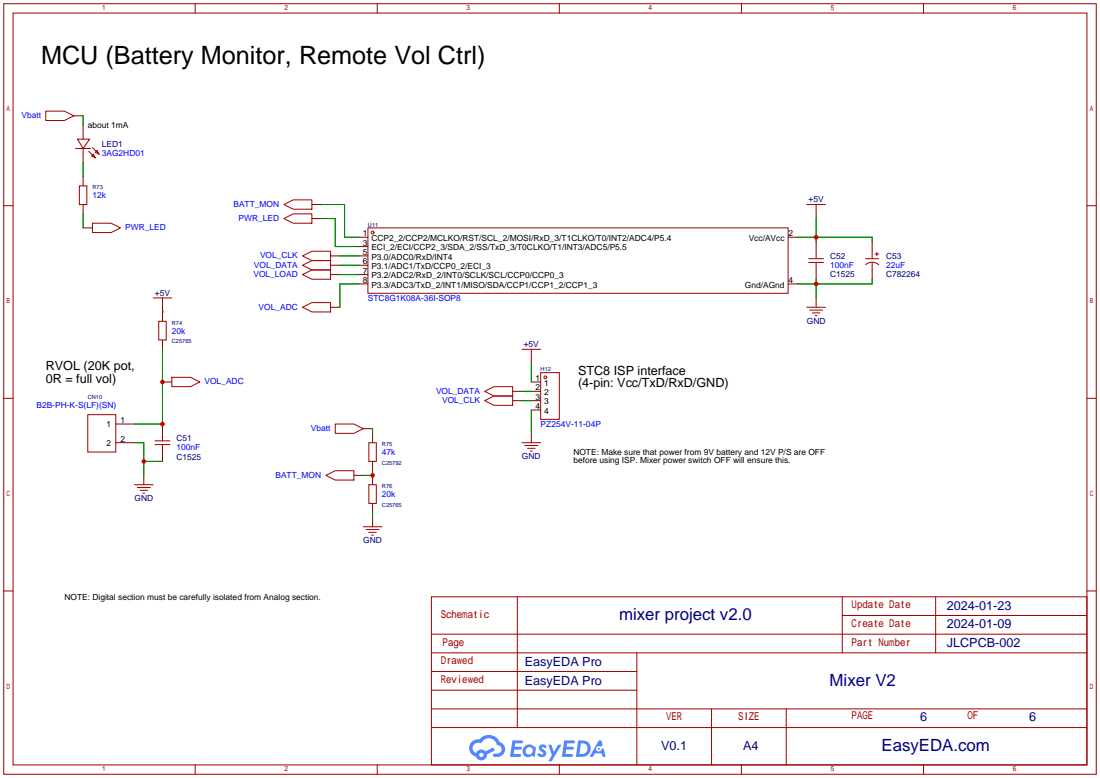
[picture p83: page 6]

STC8 ISP interface
(4-pin: Vcc/TxD/RxD/GND)

NOTE: Make sure that power from 9V battery and 12V P/S are OFF
before using ISP. Mixer power switch OFF will ensure this.

NOTE: Digital section must be carefully isolated from Analog section.
