mpogue2/ladybug-mixer/LB-102/V3/Main Board/SCH_mixer project v2.2_2024-04-04_FABBED.pdf

# Microphone preamp, Mic #1

# Single "Tilt" (+/-16dB)

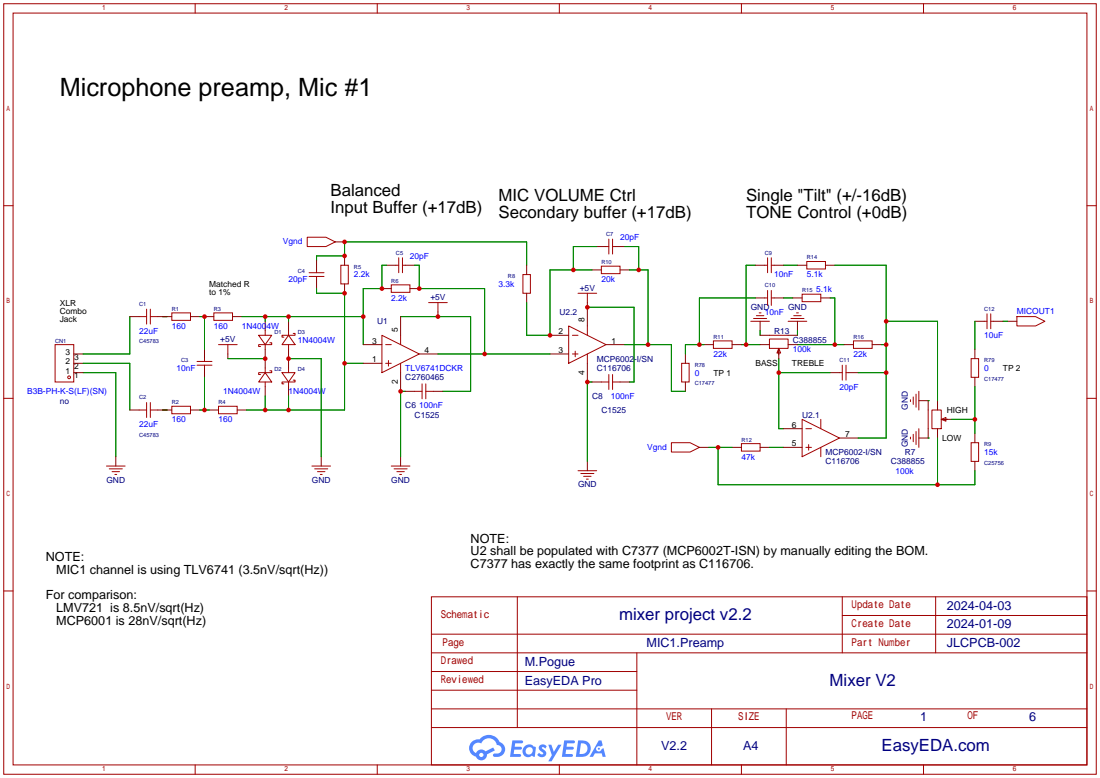
[picture p84: page 1]

NOTE:
U2 shall be populated with C7377 (MCP6002T-ISN) by manually editing the BOM.
C7377 has exactly the same footprint as C116706.

MIC1 channel is using TLV6741 (3.5nV/sqrt(Hz))
For comparison:
LMV721 is 8.5nV/sqrt(Hz)
MCP6001 is 28nV/sqrt(Hz)

# Microphone preamp, Mic #2

# Single "Tilt" (+/-16dB)

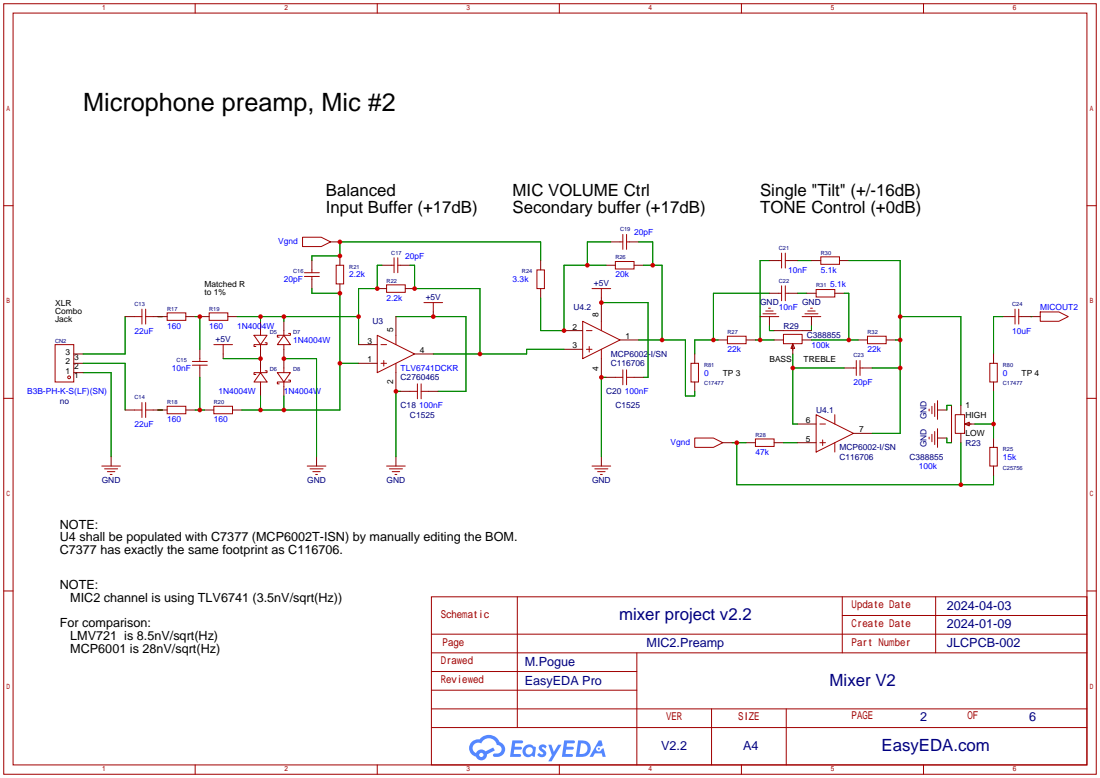
[picture p85: page 2]

NOTE:
U4 shall be populated with C7377 (MCP6002T-ISN) by manually editing the BOM.
C7377 has exactly the same footprint as C116706.

MIC2 channel is using TLV6741 (3.5nV/sqrt(Hz))
For comparison:
LMV721 is 8.5nV/sqrt(Hz)
MCP6001 is 28nV/sqrt(Hz)

# Music Mixer/Preamp/Remote Vol/Main Vol Control

(source: https://www.ti.com/lit/ug/tidu034/tidu034.pdf, https://sound-au.com/project01.htm,

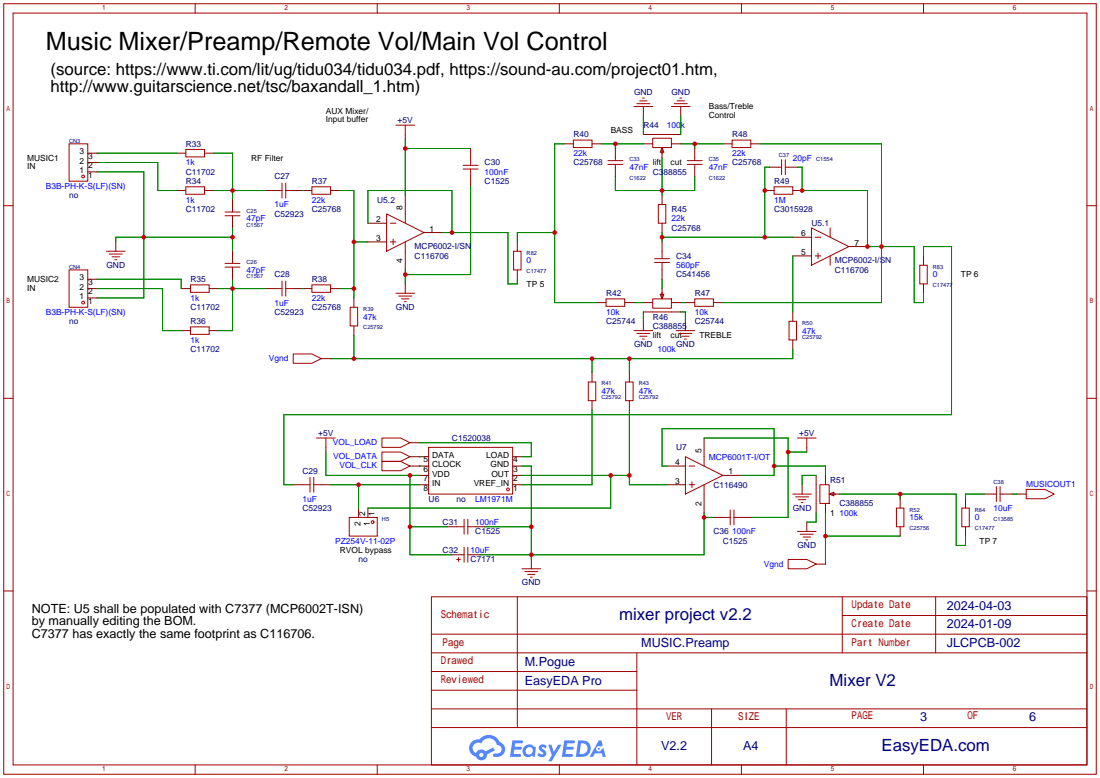
[picture p86: page 3]

http://www.guitarscience.net/tsc/baxandall_1.htm)

NOTE: U5 shall be populated with C7377 (MCP6002T-ISN)
by manually editing the BOM.
C7377 has exactly the same footprint as C116706.

# Final Mixer/Balanced output driver

# Voice/Music Mixer Voice Mixer &

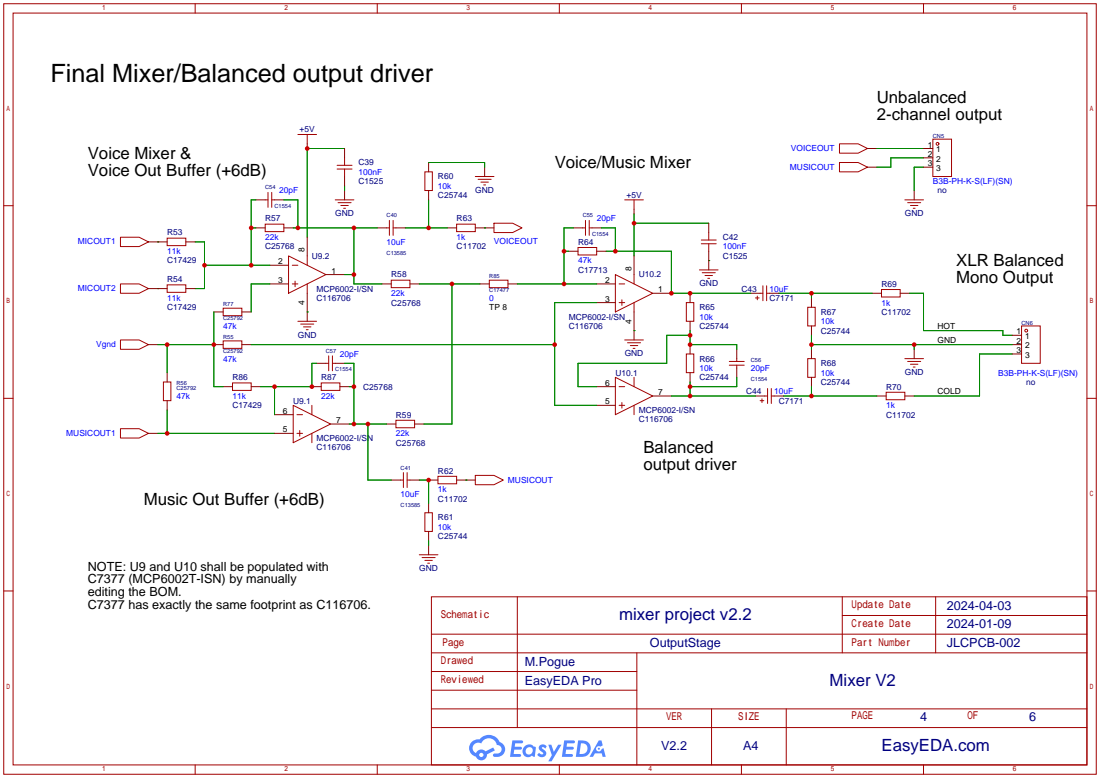
[picture p87: page 4]

NOTE: U9 and U10 shall be populated with
C7377 (MCP6002T-ISN) by manually
editing the BOM.
C7377 has exactly the same footprint as C116706.

# Input Power Management

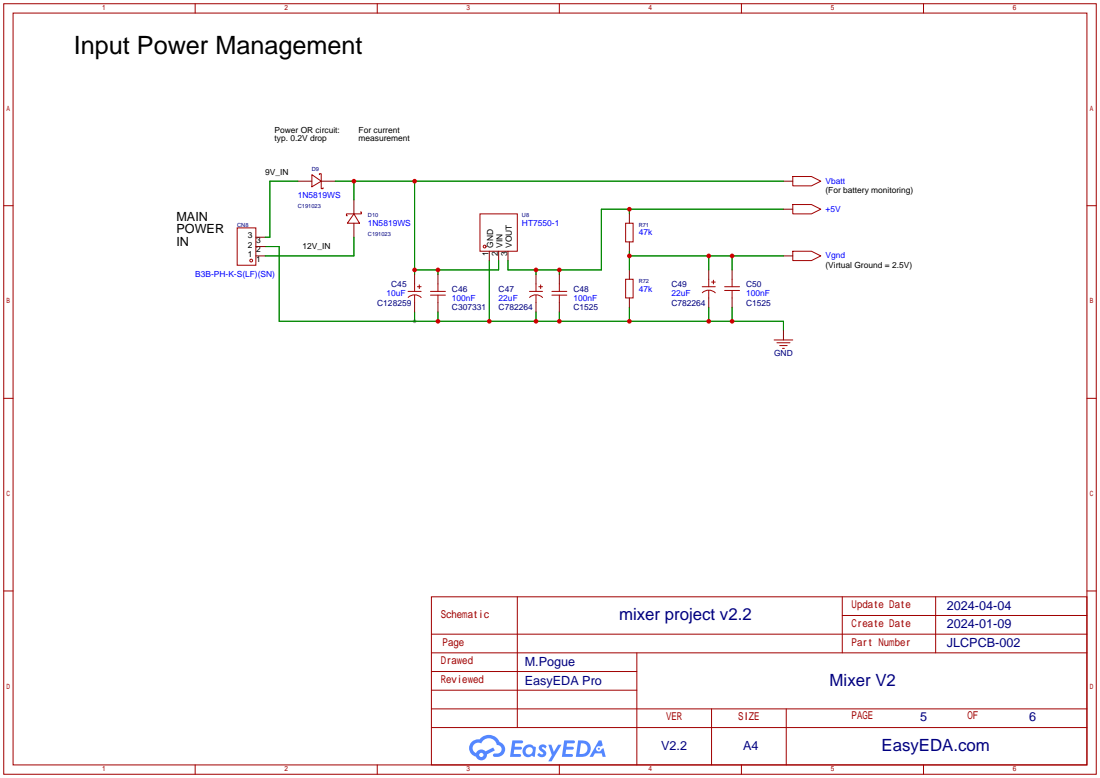
[picture p88: page 5]

# MCU (Battery Monitor, Remote Vol Ctrl)

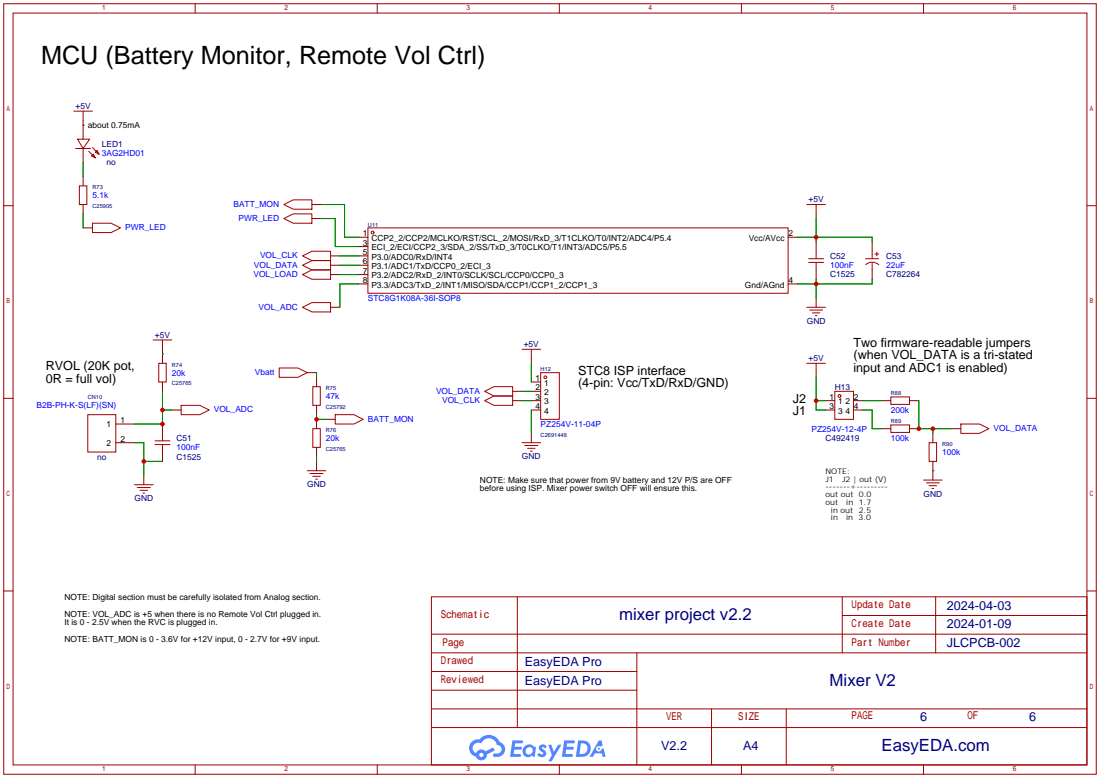
[picture p89: page 6]

GND
Two firmware-readable jumpers
(when VOL_DATA is a tri-stated
input and ADC1 is enabled)

STC8 ISP interface
(4-pin: Vcc/TxD/RxD/GND)

NOTE: Make sure that power from 9V battery and 12V P/S are OFF
before using ISP. Mixer power switch OFF will ensure this.

NOTE: Digital section must be carefully isolated from Analog section.
NOTE: VOL_ADC is +5 when there is no Remote Vol Ctrl plugged in.
It is 0 - 2.5V when the RVC is plugged in.
NOTE: BATT_MON is 0 - 3.6V for +12V input, 0 - 2.7V for +9V input.
