mpogue2/ladybug-mixer/LB-102/V2/LTspice/PDF/NewBalancedMicInput_V2.4.asc.pdf

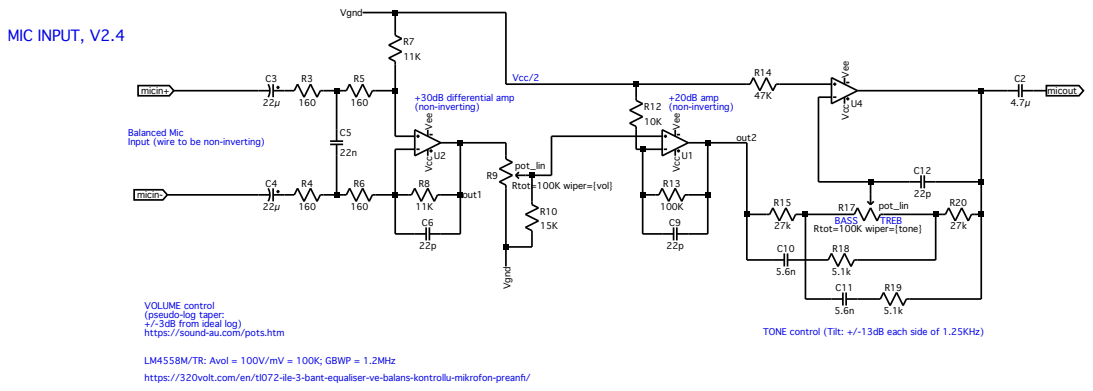
[picture p90: page 1]

Balanced Mic
Input (wire to be non-inverting)

VOLUME control
(pseudo-log taper:
+/-3dB from ideal log)
https://sound-au.com/pots.htm

TONE control (Tilt: +/-13dB each side of 1.25KHz)

LM4558M/TR: Avol = 100V/mV = 100K; GBWP = 1.2MHz
https://320volt.com/en/tl072-ile-3-bant-equaliser-ve-balans-kontrollu-mikrofon-preanfi/
