mpogue2/ladybug-mixer/LB-102/V2/LTspice/PDF/NewFinalMixer_V2.4.asc.pdf

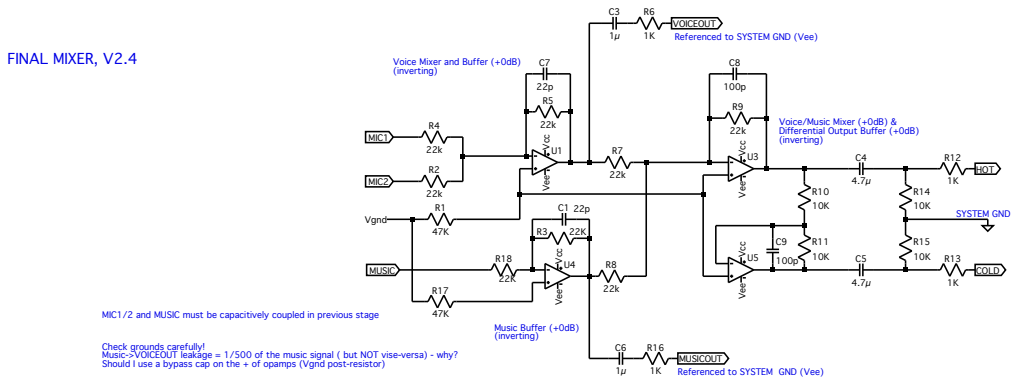
[picture p91: page 1]

Voice Mixer and Buffer (+0dB)
(inverting)

MIC1/2 and MUSIC must be capacitively coupled in previous stage

Check grounds carefully!
Music->VOICEOUT leakage = 1/500 of the music signal ( but NOT vise-versa) - why?
Should I use a bypass cap on the + of opamps (Vgnd post-resistor)
