mpogue2/ladybug-mixer/LB-102/V2/LTspice/PDF/NewMusicInput_V2.4.asc.pdf

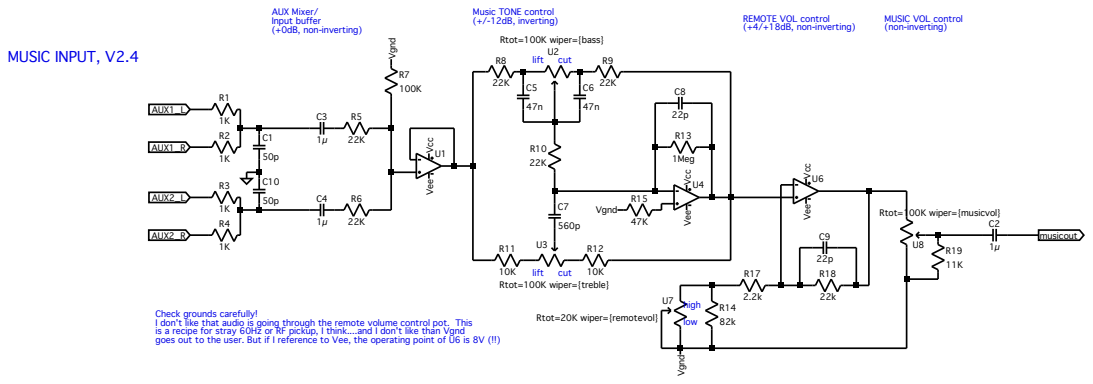
[picture p92: page 1]

Check grounds carefully!
I don't like that audio is going through the remote volume control pot. This
is a recipe for stray 60Hz or RF pickup, I think....and I don't like than Vgnd
goes out to the user. But if I reference to Vee, the operating point of U6 is 8V (!!)
