mpogue2/ladybug-mixer/LB-102/V3/Main Board/PCB_PCB2_2024-04-04_FABBED.pdf

# TREB BASS

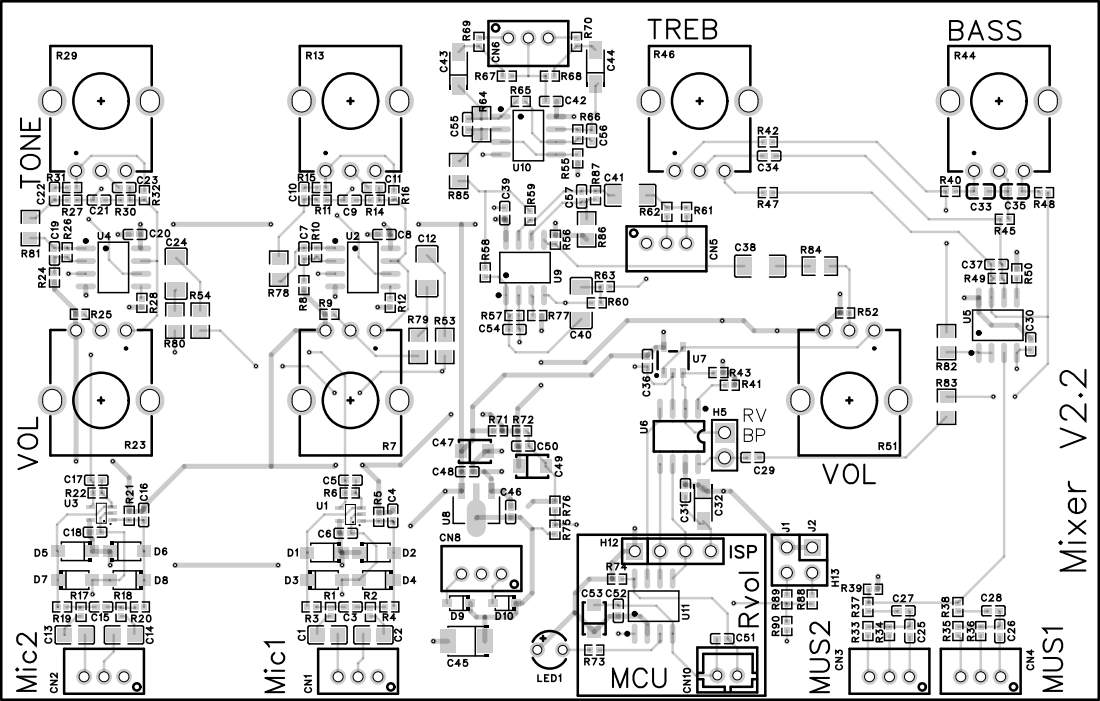
[picture p93: page 1]

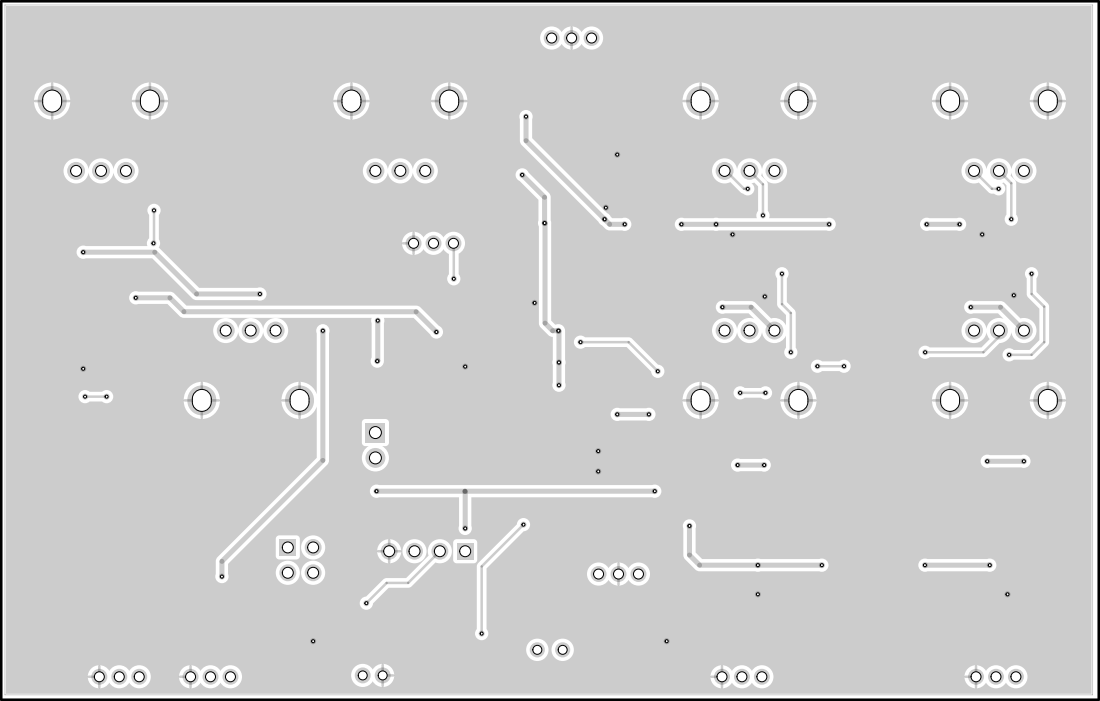
[picture p94: page 2]

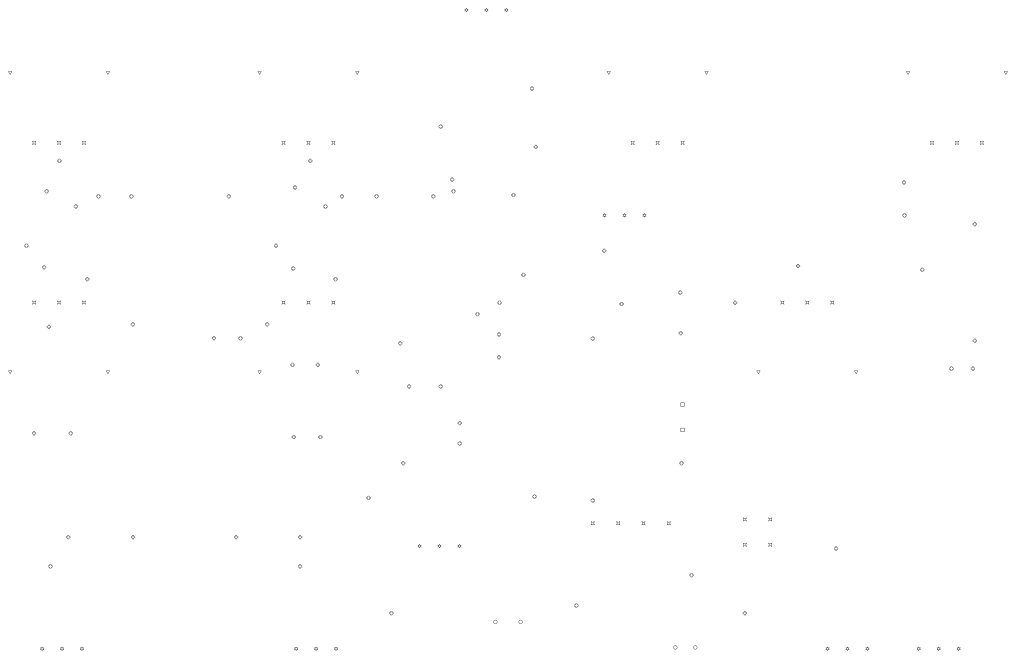
[picture p95: page 3]

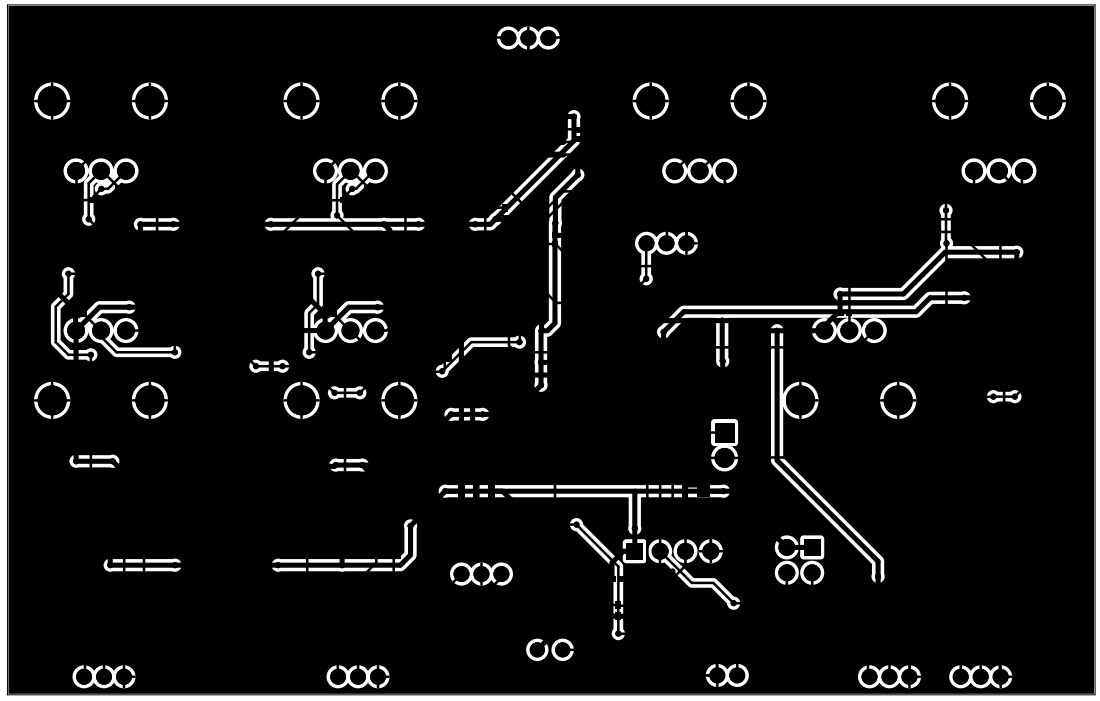
[picture p96: page 4]
