mpogue2/ladybug-mixer/LB-102/V2/LTspice/PDF/NewTopLevel_V2.4.asc.pdf

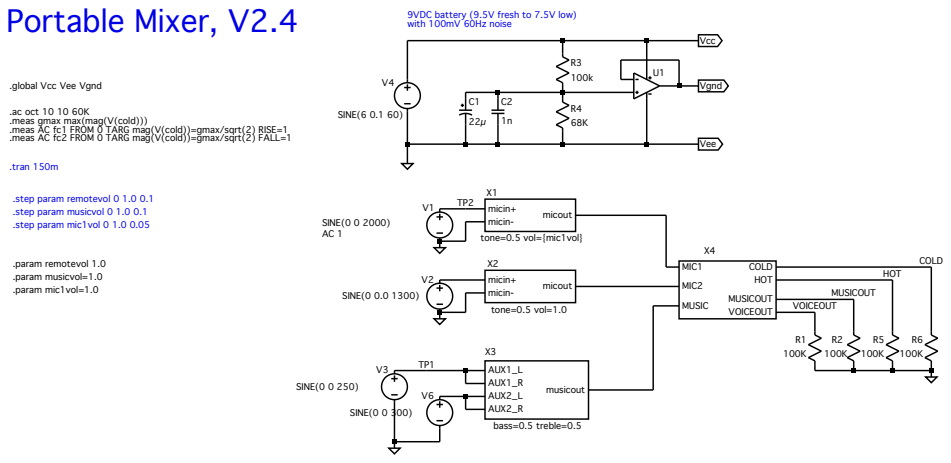
[picture p97: page 1]

.global Vcc Vee Vgnd

.ac oct 10 10 60K
.meas gmax max(mag(V(cold)))
.meas AC fc1 FROM 0 TARG mag(V(cold))=gmax/sqrt(2) RISE=1
.meas AC fc2 FROM 0 TARG mag(V(cold))=gmax/sqrt(2) FALL=1
